esp-cpp/esp-box-emu/boxart/source/aladdin-genesis.jpg

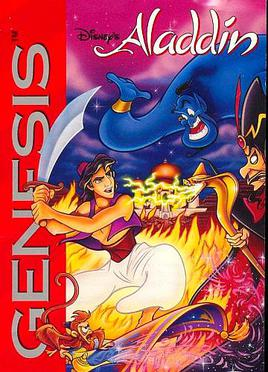
boxart/source/aladdin-genesis.jpg
