esp-cpp/esp-box-emu/boxart/source/aladdin-gg.jpg

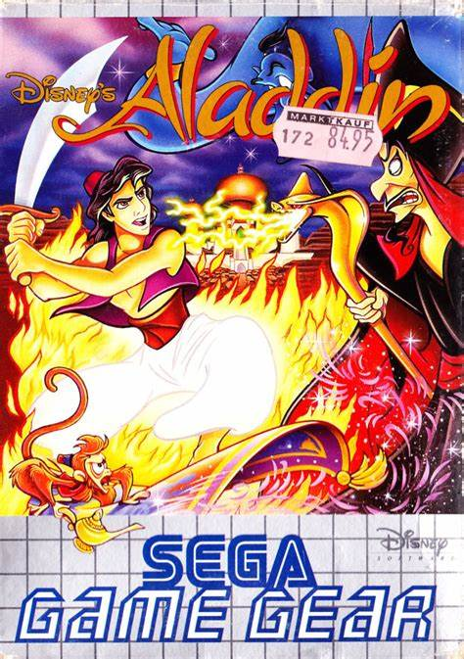
boxart/source/aladdin-gg.jpg
