esp-cpp/esp-box-emu/boxart/source/batman-forever-gg.jpg

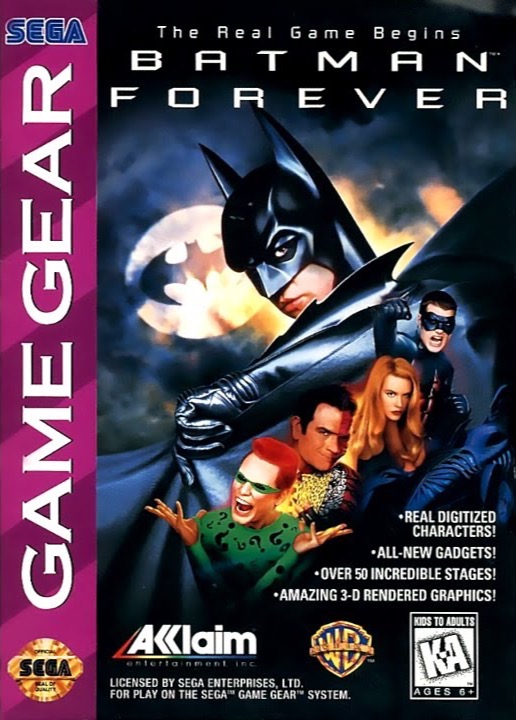
boxart/source/batman-forever-gg.jpg
