esp-cpp/esp-box-emu/boxart/source/batman_the_animated_series.jpg

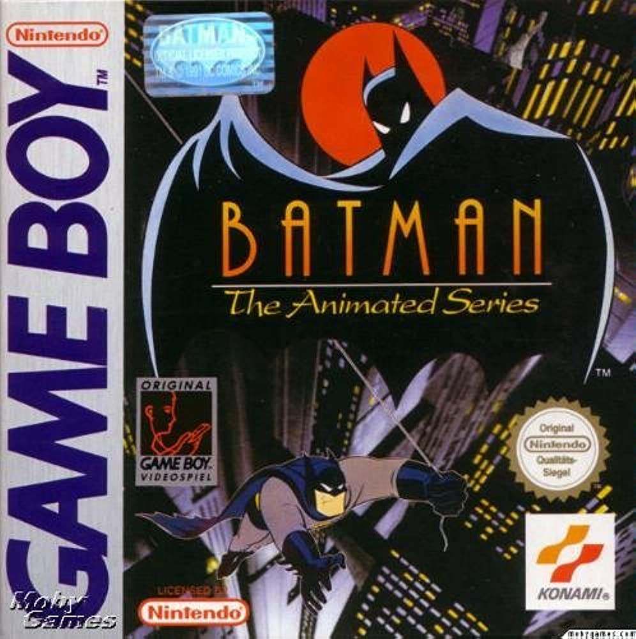
boxart/source/batman_the_animated_series.jpg
