esp-cpp/esp-box-emu/boxart/source/castle-of-illusion-gg.jpg

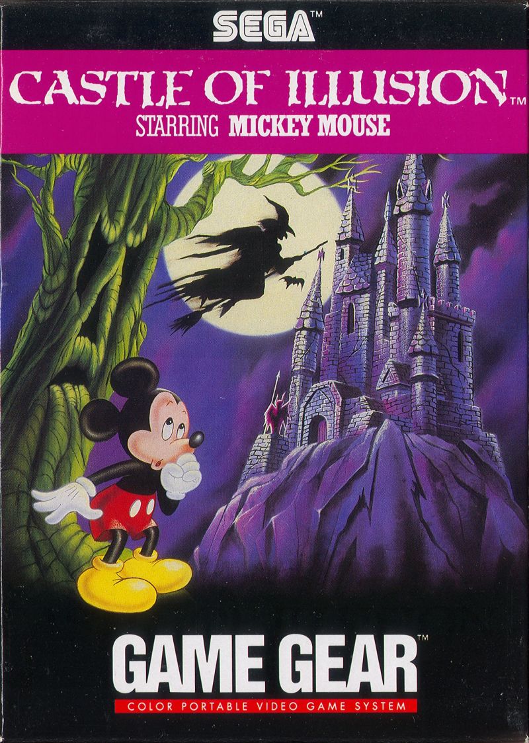
boxart/source/castle-of-illusion-gg.jpg
