esp-cpp/esp-box-emu/boxart/source/chrono_trigger.jpg

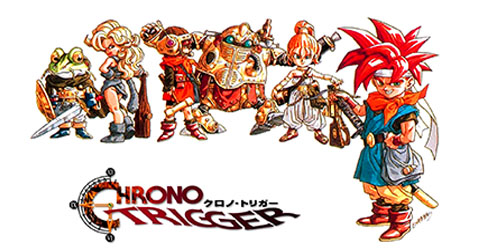
boxart/source/chrono_trigger.jpg
