esp-cpp/esp-box-emu/boxart/source/donkey_kong_country.jpg

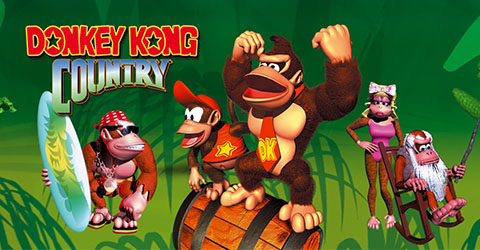
boxart/source/donkey_kong_country.jpg
