esp-cpp/esp-box-emu/boxart/source/doom_2_boxart.jpg

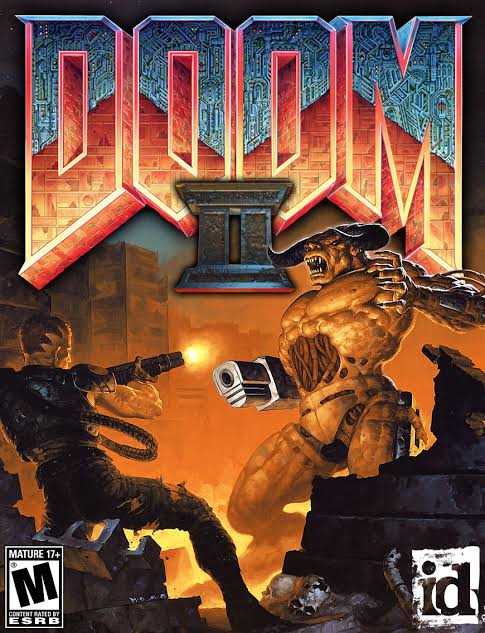
boxart/source/doom_2_boxart.jpg
