esp-cpp/esp-box-emu/boxart/source/doom_boxart.jpg

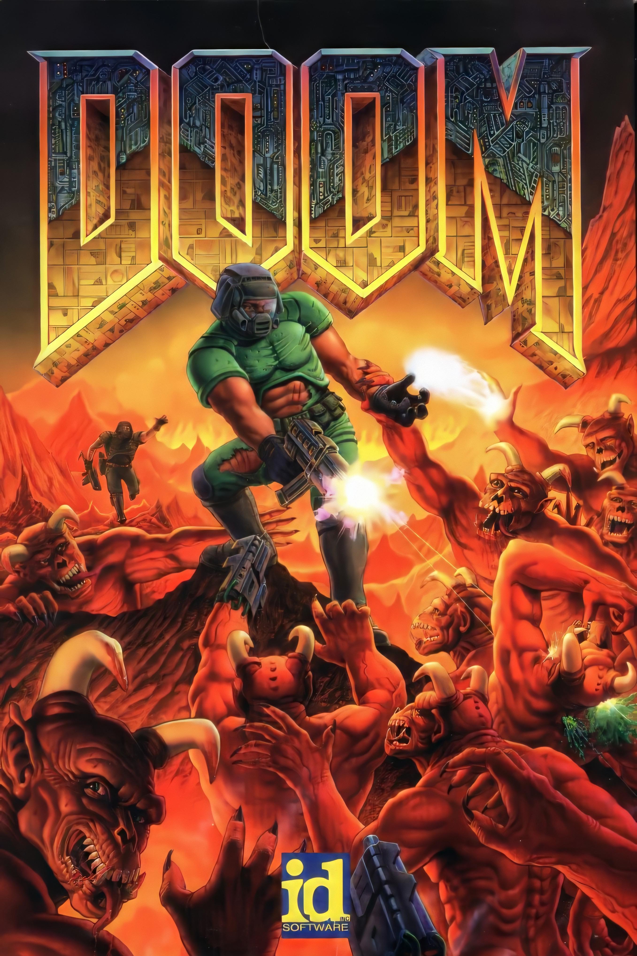
boxart/source/doom_boxart.jpg
