esp-cpp/esp-box-emu/boxart/source/doom_ultimate_boxart.jpg

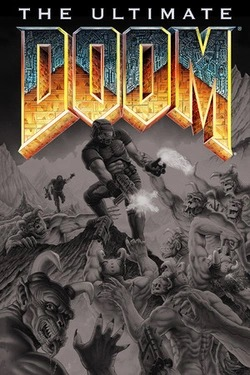
boxart/source/doom_ultimate_boxart.jpg
