esp-cpp/esp-box-emu/boxart/source/duck_tales.jpg

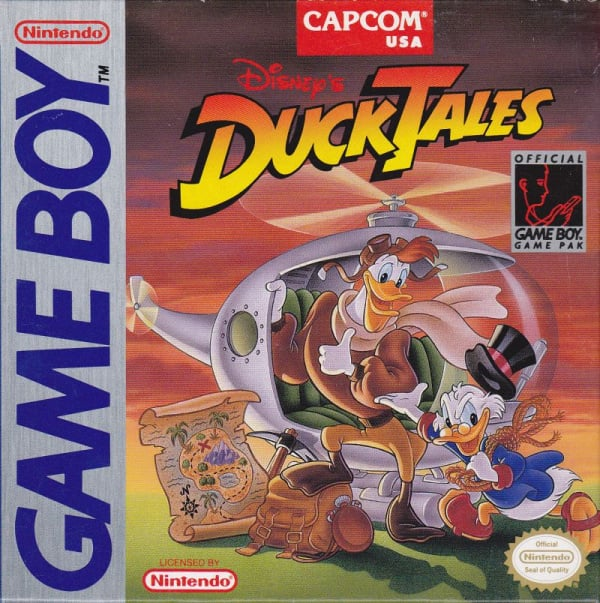
boxart/source/duck_tales.jpg
