esp-cpp/esp-box-emu/boxart/source/ducktales_nes.jpg

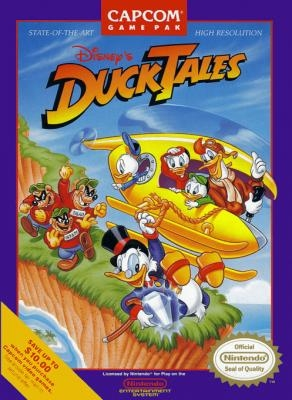
boxart/source/ducktales_nes.jpg
