esp-cpp/esp-box-emu/boxart/source/final_fantasy.jpg

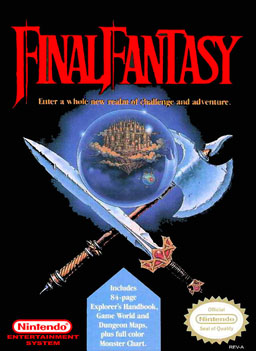
boxart/source/final_fantasy.jpg
