esp-cpp/esp-box-emu/boxart/source/final_fantasy_adventure.jpg

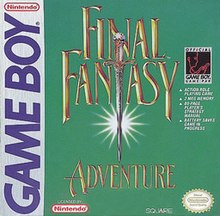
boxart/source/final_fantasy_adventure.jpg
