esp-cpp/esp-box-emu/boxart/source/final_fantasy_ii.jpg

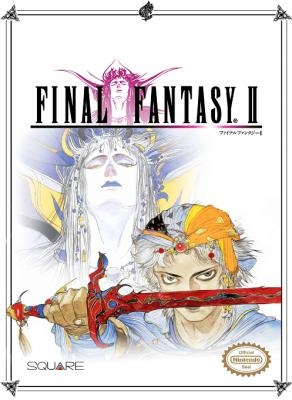
boxart/source/final_fantasy_ii.jpg
