esp-cpp/esp-box-emu/boxart/source/final_fantasy_iii.jpg

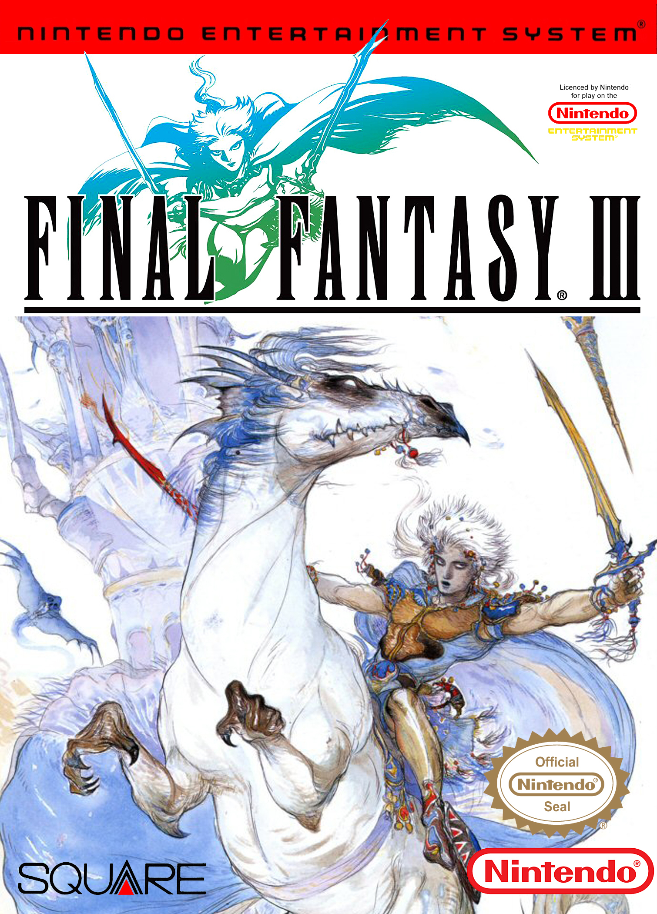
boxart/source/final_fantasy_iii.jpg
