esp-cpp/esp-box-emu/boxart/source/ghouls-n-ghosts-sms.jpg

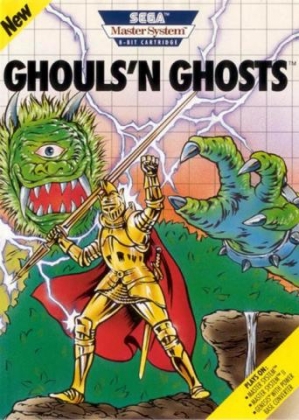
boxart/source/ghouls-n-ghosts-sms.jpg
