esp-cpp/esp-box-emu/boxart/source/harvest_moon.jpg

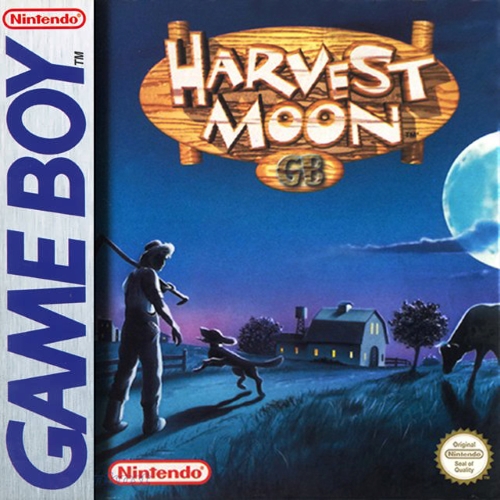
boxart/source/harvest_moon.jpg
