esp-cpp/esp-box-emu/boxart/source/harvest_moon_gbc.jpg

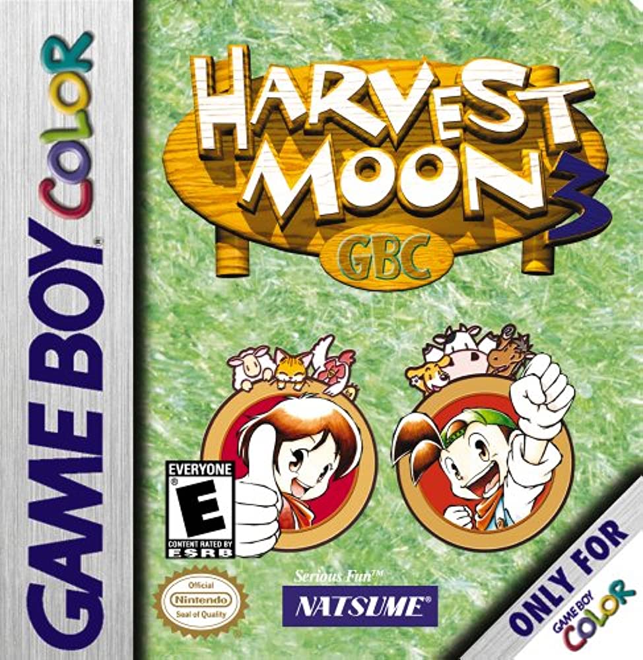
boxart/source/harvest_moon_gbc.jpg
