esp-cpp/esp-box-emu/boxart/source/jurassic-park-gg.jpg

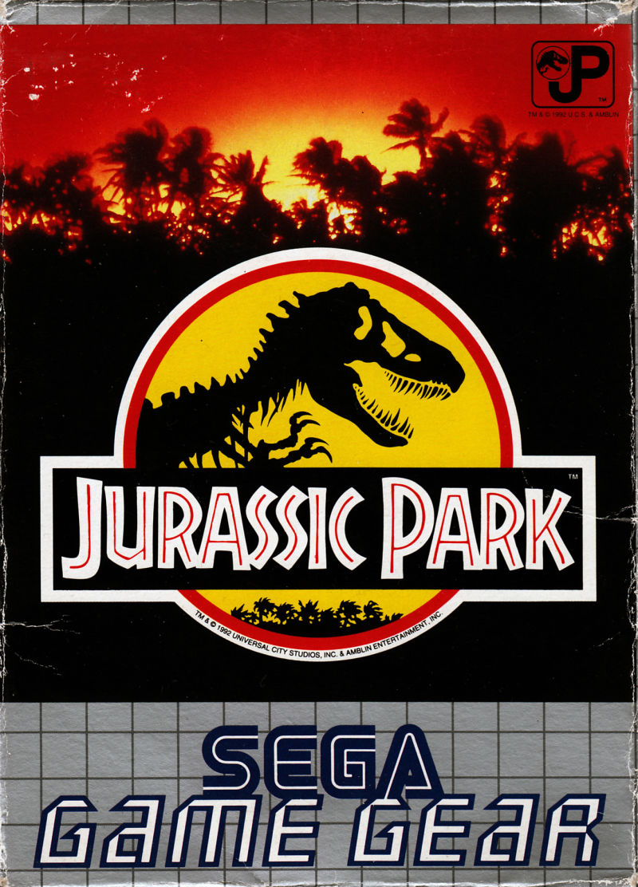
boxart/source/jurassic-park-gg.jpg
