esp-cpp/esp-box-emu/boxart/source/lion-king-genesis.jpg

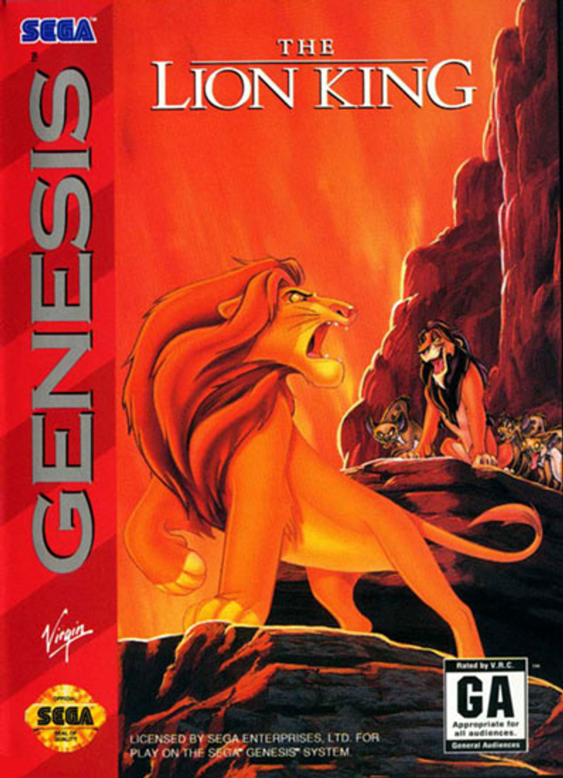
boxart/source/lion-king-genesis.jpg
