esp-cpp/esp-box-emu/boxart/source/mario.jpg

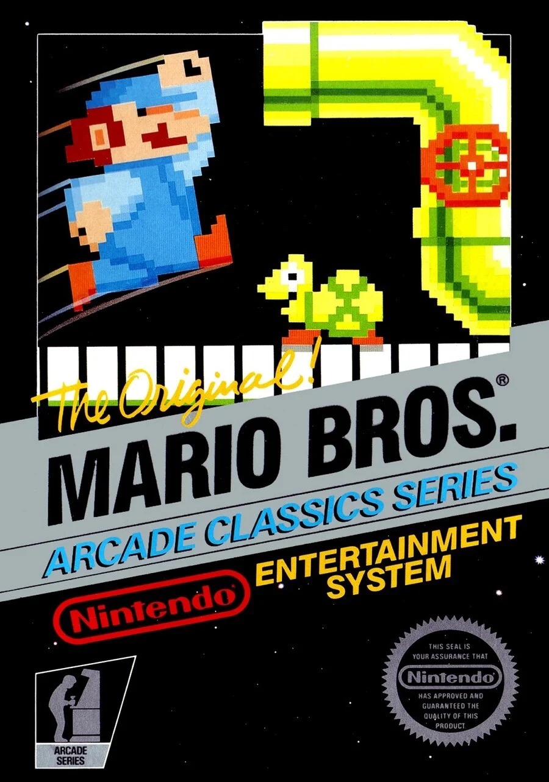
boxart/source/mario.jpg
