esp-cpp/esp-box-emu/boxart/source/mario_golf.jpg

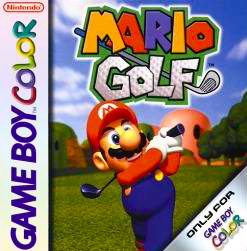
boxart/source/mario_golf.jpg
