esp-cpp/esp-box-emu/boxart/source/mario_open_golf.jpg

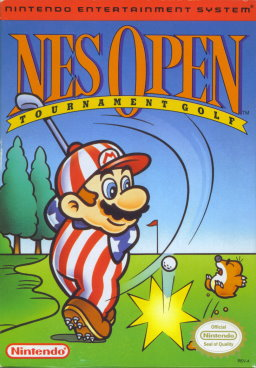
boxart/source/mario_open_golf.jpg
