esp-cpp/esp-box-emu/boxart/source/mario_tennis.jpg

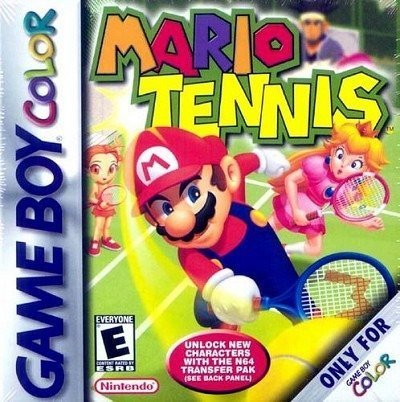
boxart/source/mario_tennis.jpg
