esp-cpp/esp-box-emu/boxart/source/megaman1.jpg

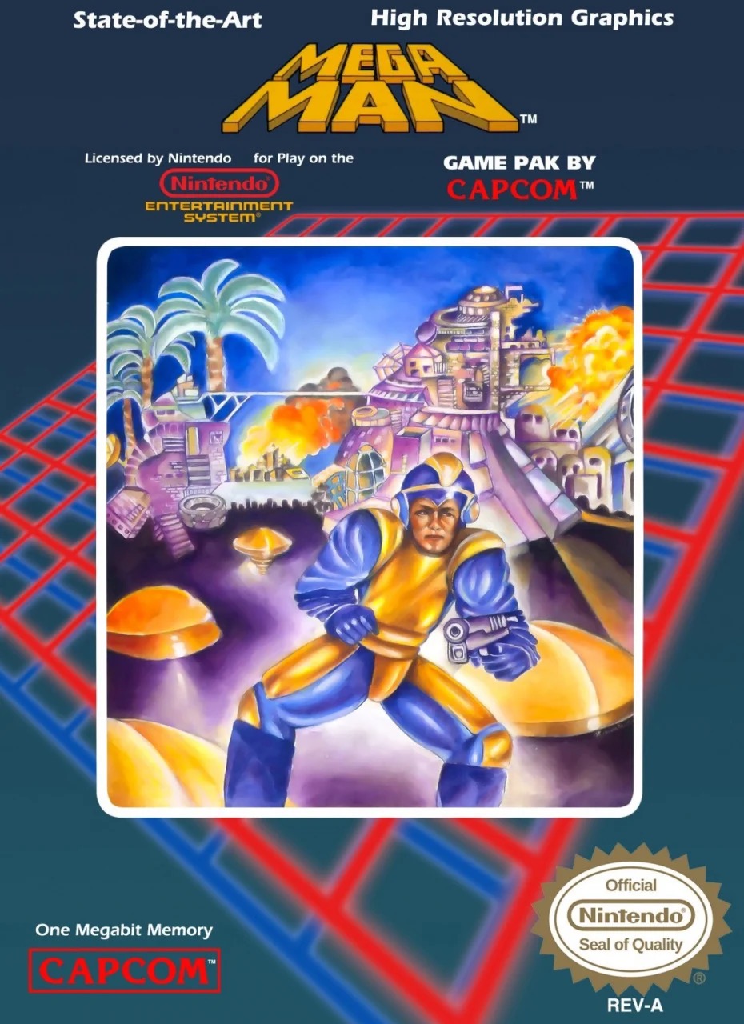
boxart/source/megaman1.jpg
