esp-cpp/esp-box-emu/boxart/source/metal_gear.jpg

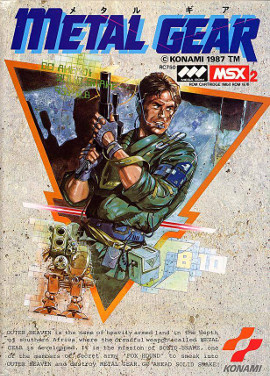
boxart/source/metal_gear.jpg
