esp-cpp/esp-box-emu/boxart/source/metal_gear_solid.jpg

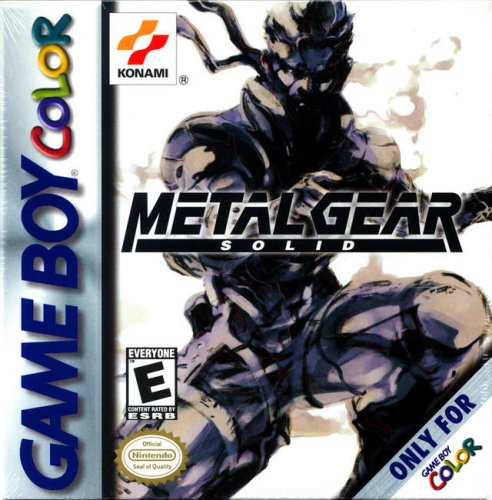
boxart/source/metal_gear_solid.jpg
