esp-cpp/esp-box-emu/boxart/source/metroid1.jpg

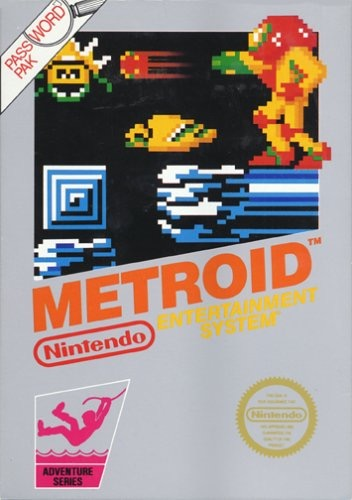
boxart/source/metroid1.jpg
