esp-cpp/esp-box-emu/boxart/source/metroid_2_return_of_samus.jpg

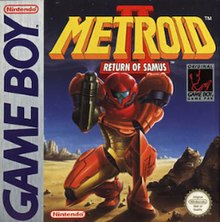
boxart/source/metroid_2_return_of_samus.jpg
