esp-cpp/esp-box-emu/boxart/source/mg1msxartwork.jpg

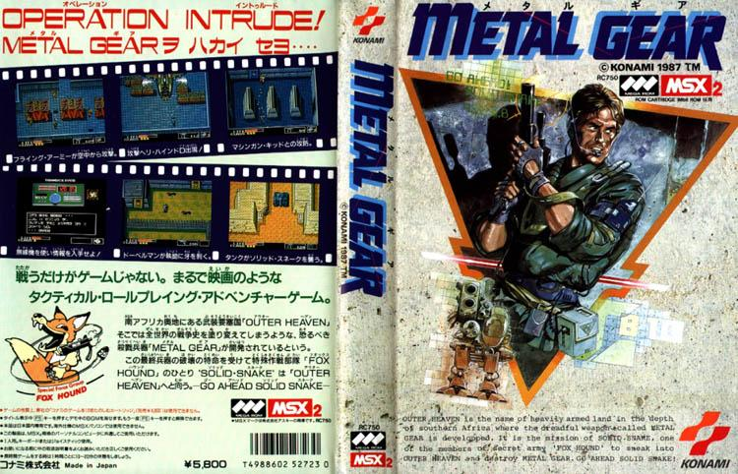
boxart/source/mg1msxartwork.jpg
