esp-cpp/esp-box-emu/boxart/source/mg2msxartwork.jpg

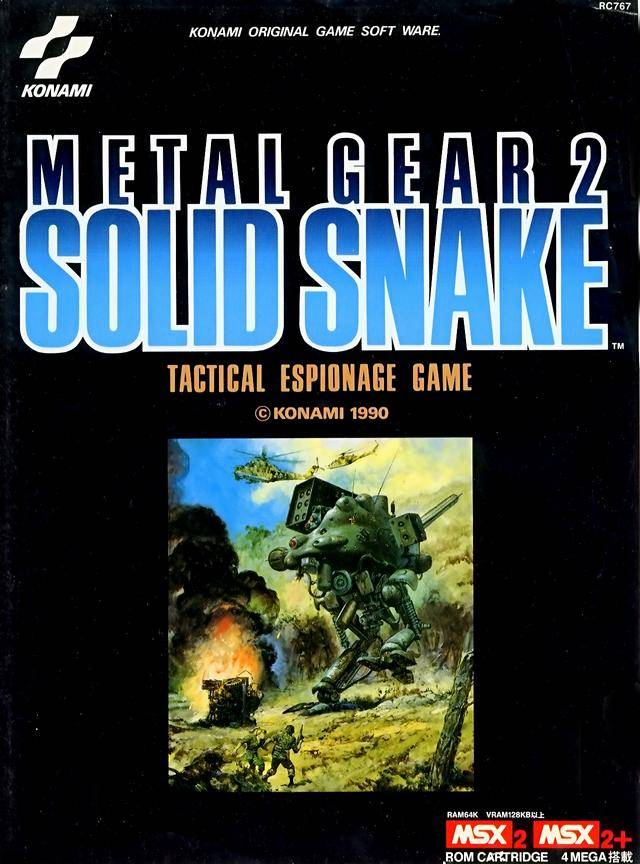
boxart/source/mg2msxartwork.jpg
