esp-cpp/esp-box-emu/boxart/source/Ninja+Gaiden+(Europe)-sms.jpg

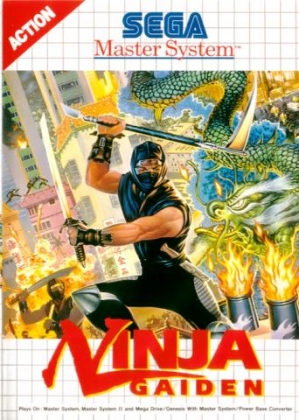
boxart/source/Ninja+Gaiden+(Europe)-sms.jpg
