esp-cpp/esp-box-emu/boxart/source/Out+Run+(Europe)-gg.jpg

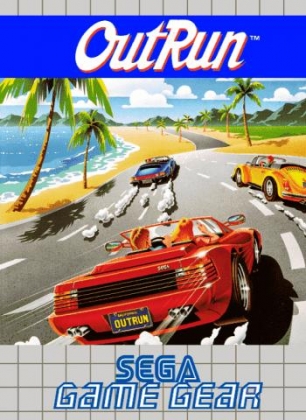
boxart/source/Out+Run+(Europe)-gg.jpg
