esp-cpp/esp-box-emu/boxart/source/Out+Run+(World)-sms.jpg

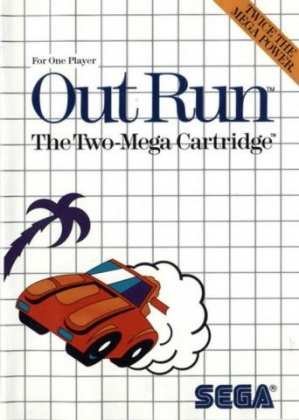
boxart/source/Out+Run+(World)-sms.jpg
