esp-cpp/esp-box-emu/boxart/source/Out+Run+Europa+gg.jpg

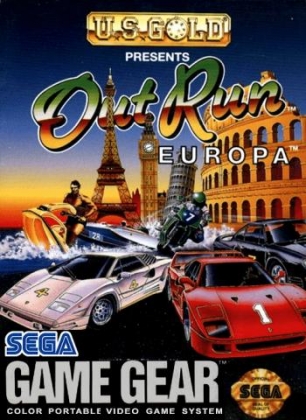
boxart/source/Out+Run+Europa+gg.jpg
