esp-cpp/esp-box-emu/boxart/source/pokemon_blue.jpg

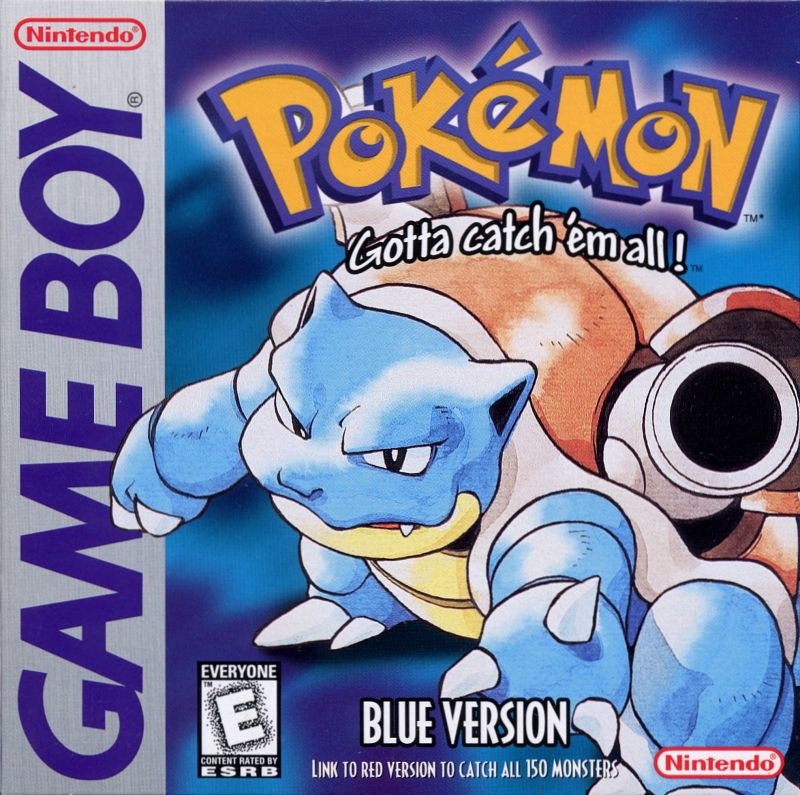
boxart/source/pokemon_blue.jpg
