esp-cpp/esp-box-emu/boxart/source/pokemon_crystal.jpg

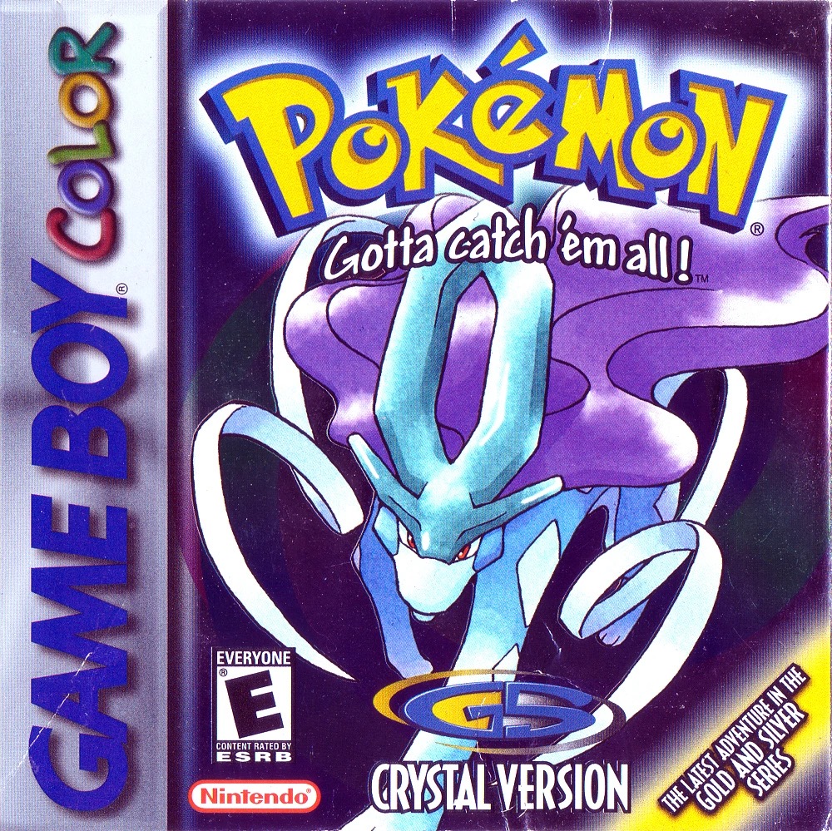
boxart/source/pokemon_crystal.jpg
