esp-cpp/esp-box-emu/boxart/source/pokemon_red.jpg

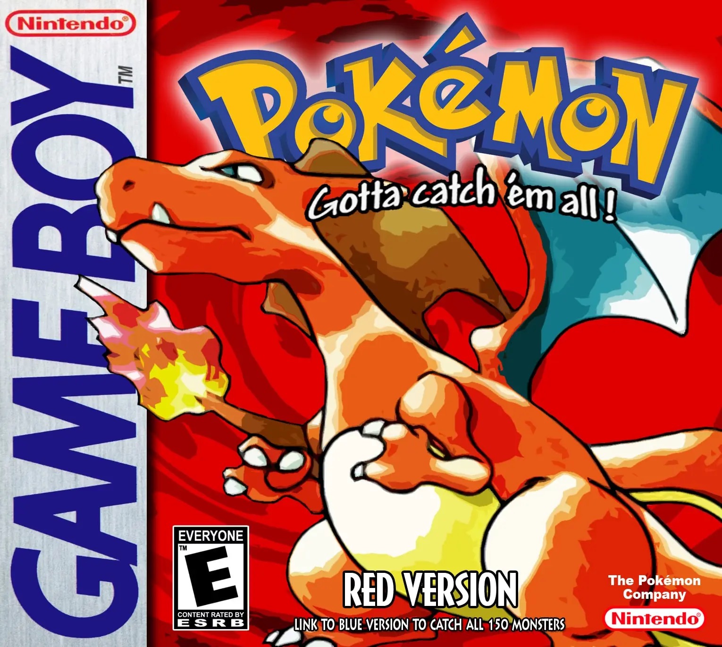
boxart/source/pokemon_red.jpg
