esp-cpp/esp-box-emu/boxart/source/R-Type-sms.jpg

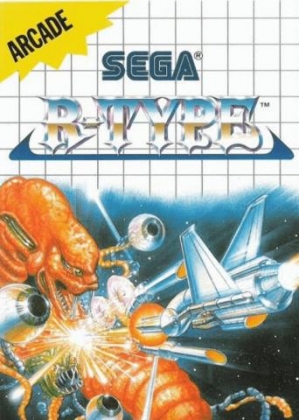
boxart/source/R-Type-sms.jpg
