esp-cpp/esp-box-emu/boxart/source/river-city-ransom.jpg

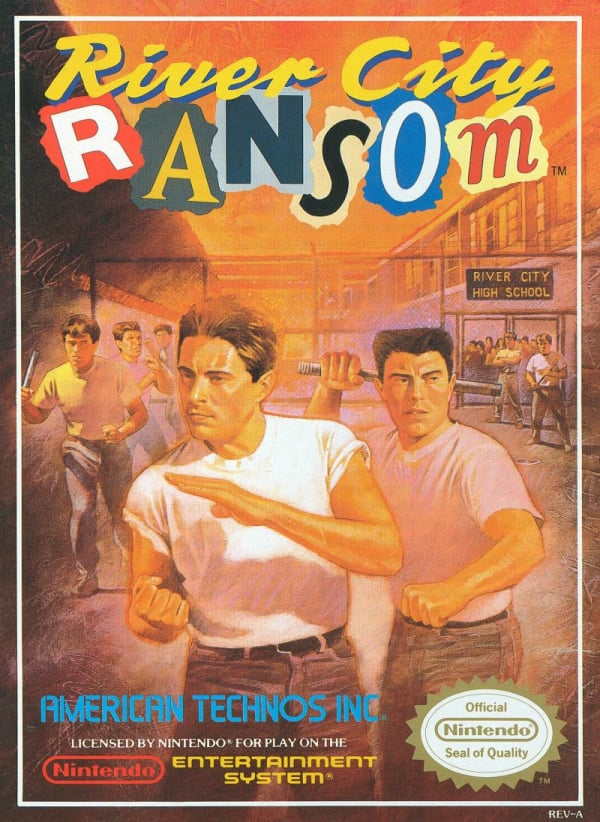
boxart/source/river-city-ransom.jpg
