esp-cpp/esp-box-emu/boxart/source/Road+Rash+(USA)-gg.jpg

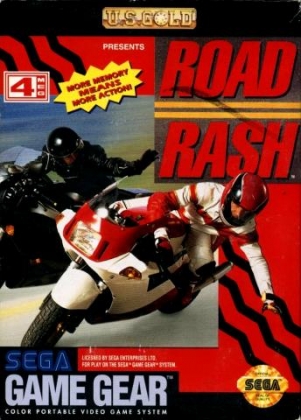
boxart/source/Road+Rash+(USA)-gg.jpg
