esp-cpp/esp-box-emu/boxart/source/shantae.jpg

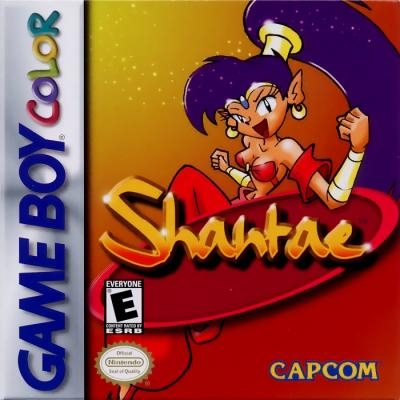
boxart/source/shantae.jpg
