esp-cpp/esp-box-emu/boxart/source/sonic-1-genesis.jpg

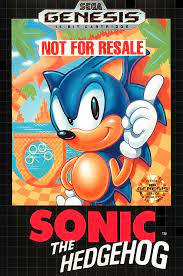
boxart/source/sonic-1-genesis.jpg
