esp-cpp/esp-box-emu/boxart/source/sonic-2-genesis.jpg

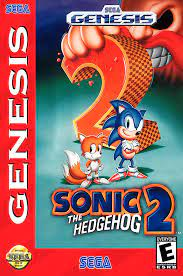
boxart/source/sonic-2-genesis.jpg
