esp-cpp/esp-box-emu/boxart/source/sonic-3-and-knuckles.jpg

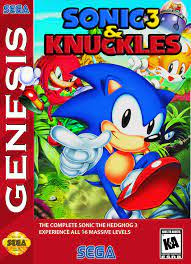
boxart/source/sonic-3-and-knuckles.jpg
