esp-cpp/esp-box-emu/boxart/source/sonic-3-genesis.jpg

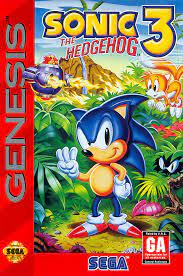
boxart/source/sonic-3-genesis.jpg
