esp-cpp/esp-box-emu/boxart/source/sonic-and-knuckles-genesis.jpg

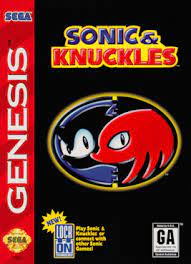
boxart/source/sonic-and-knuckles-genesis.jpg
