esp-cpp/esp-box-emu/boxart/source/sonic-the-hedgehog-2-gg.jpg

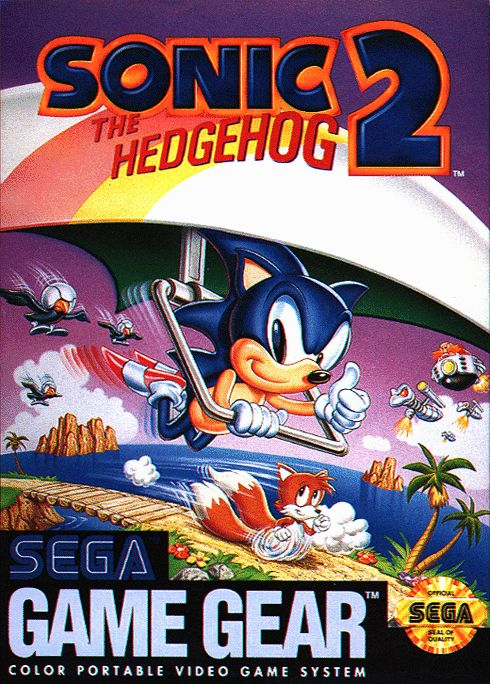
boxart/source/sonic-the-hedgehog-2-gg.jpg
