esp-cpp/esp-box-emu/boxart/source/sonic-the-hedgehog-2-sms.jpg

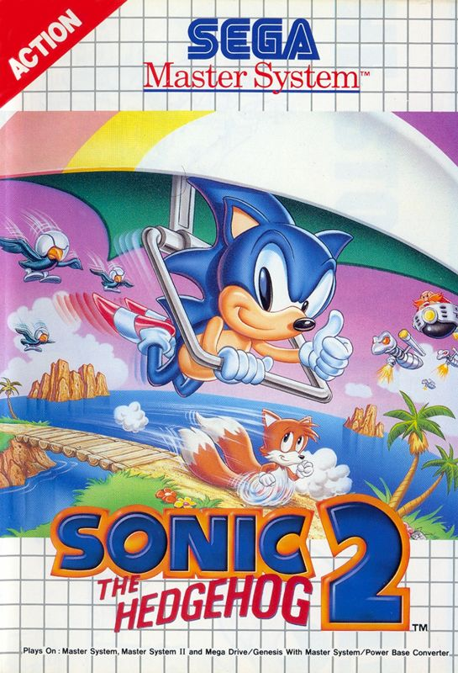
boxart/source/sonic-the-hedgehog-2-sms.jpg
