esp-cpp/esp-box-emu/boxart/source/spider-man-and-venom-maximum-carnage.jpg

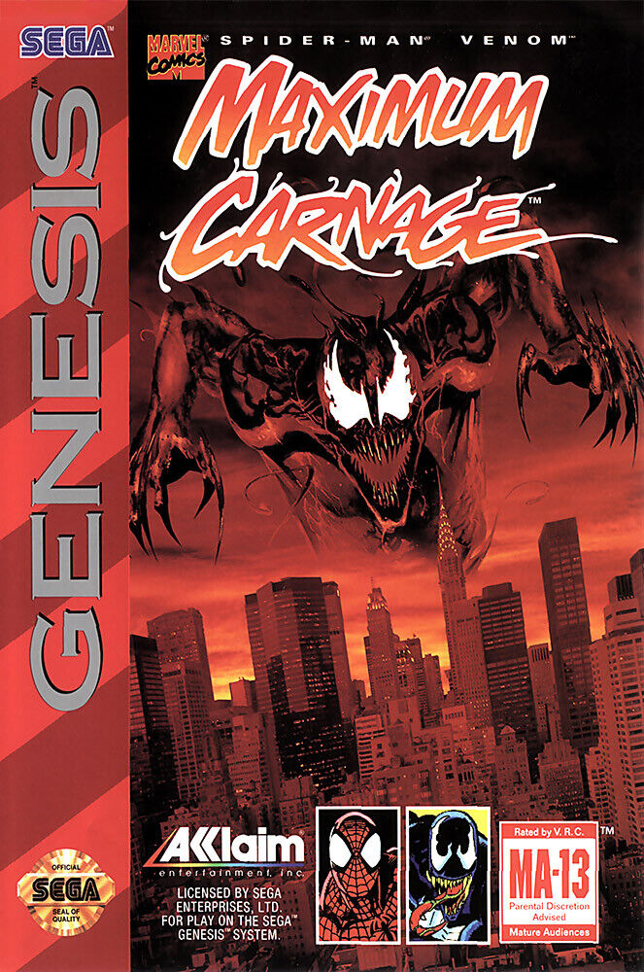
boxart/source/spider-man-and-venom-maximum-carnage.jpg
