esp-cpp/esp-box-emu/boxart/source/Star-Trek-Generations-Beyond-the-Nexus-gg.jpg

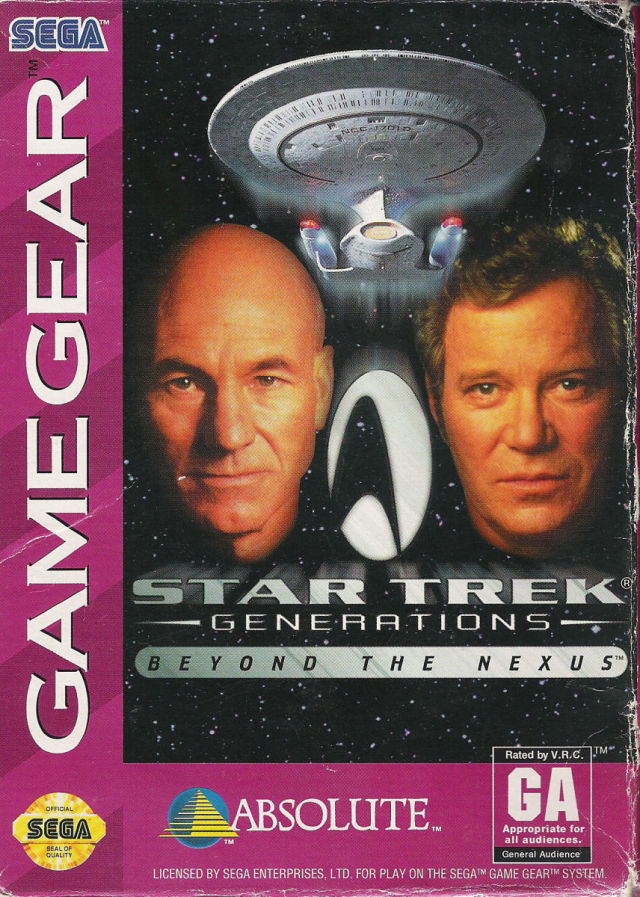
boxart/source/Star-Trek-Generations-Beyond-the-Nexus-gg.jpg
