esp-cpp/esp-box-emu/boxart/source/star_wars_arcade_32x_genesis.jpg

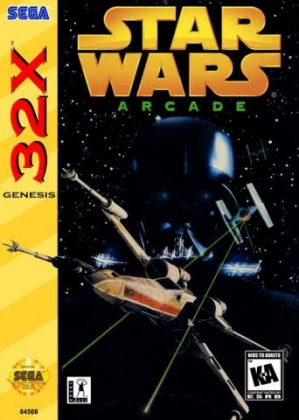
boxart/source/star_wars_arcade_32x_genesis.jpg
