esp-cpp/esp-box-emu/boxart/source/StreetsofRage2-gg.jpg

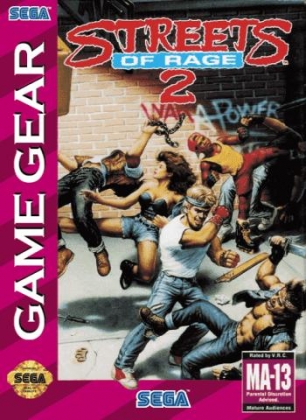
boxart/source/StreetsofRage2-gg.jpg
