esp-cpp/esp-box-emu/boxart/source/super_mario_bros_1.jpg

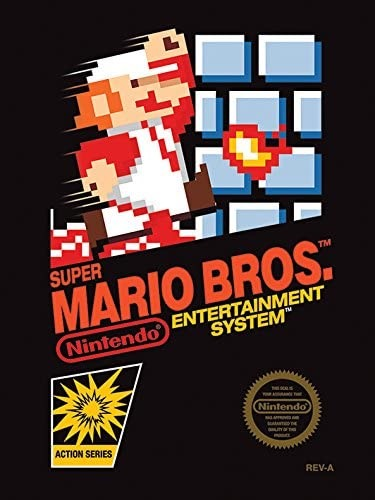
boxart/source/super_mario_bros_1.jpg
