esp-cpp/esp-box-emu/boxart/source/super_mario_bros_2.jpg

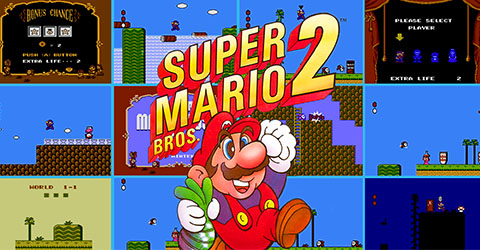
boxart/source/super_mario_bros_2.jpg
