esp-cpp/esp-box-emu/boxart/source/super_mario_bros_3.jpg

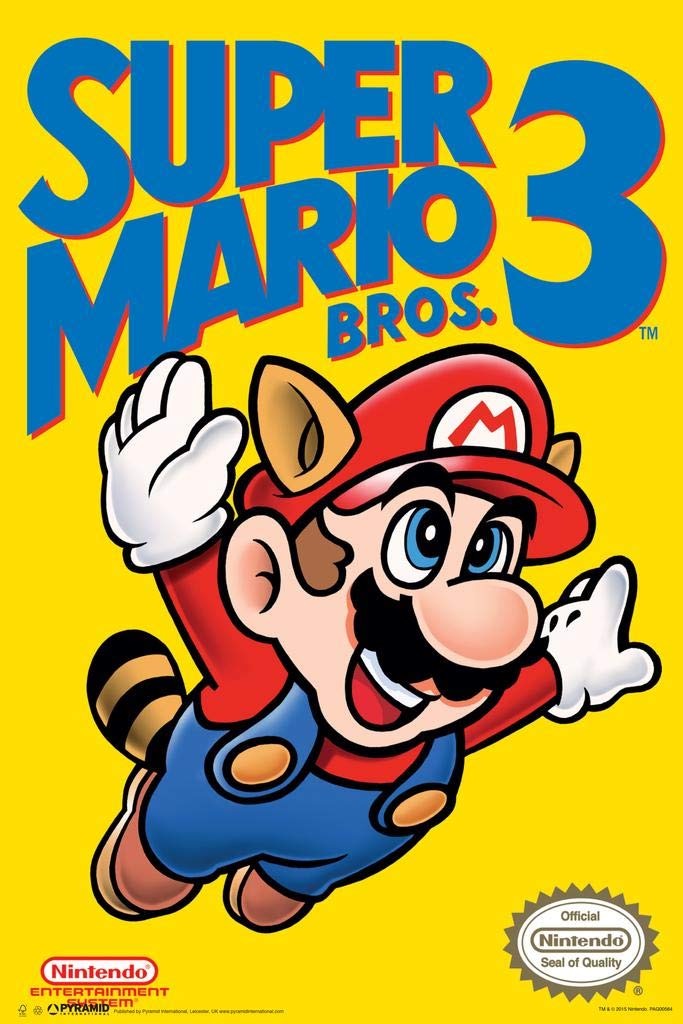
boxart/source/super_mario_bros_3.jpg
