esp-cpp/esp-box-emu/boxart/source/super_mario_bros_deluxe.jpg

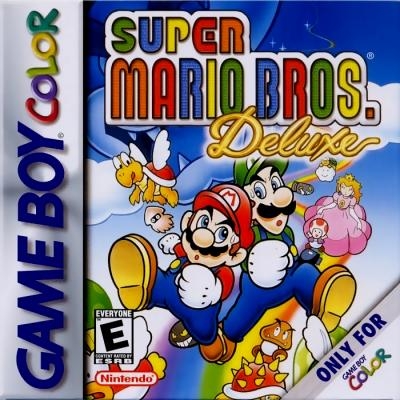
boxart/source/super_mario_bros_deluxe.jpg
