esp-cpp/esp-box-emu/boxart/source/tetris_dx.jpg

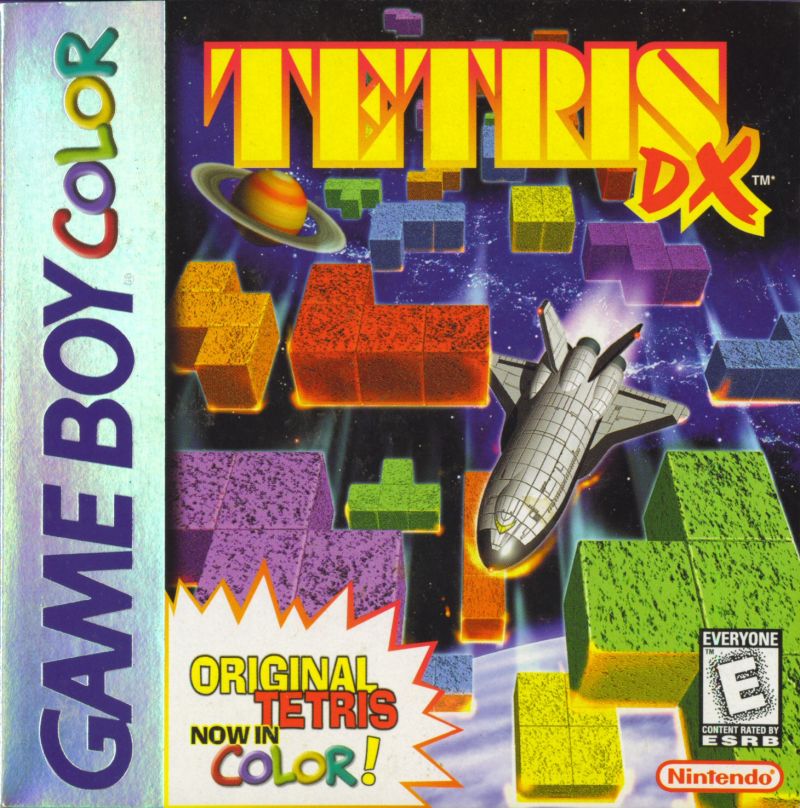
boxart/source/tetris_dx.jpg
