esp-cpp/esp-box-emu/boxart/source/The-Adventures-of-Batman-and-Robin-Game-Gear.jpg

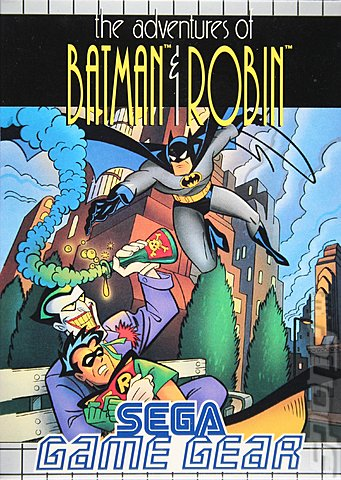
boxart/source/The-Adventures-of-Batman-and-Robin-Game-Gear.jpg
