esp-cpp/esp-box-emu/boxart/source/tloz_links_awakening.jpg

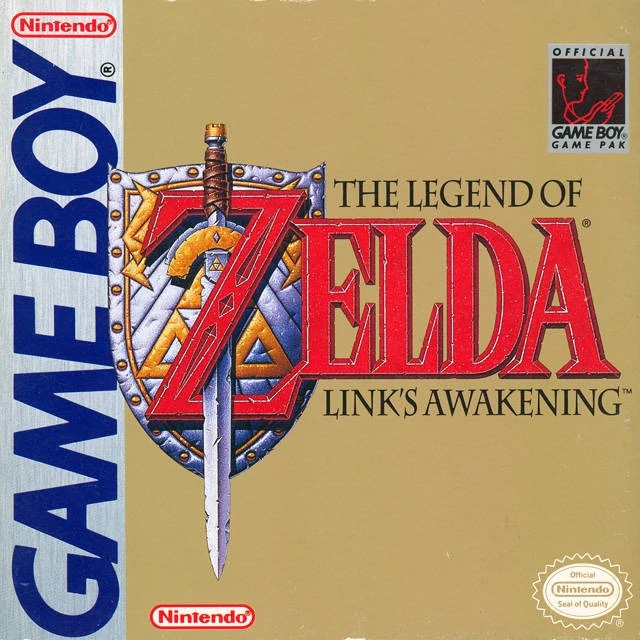
boxart/source/tloz_links_awakening.jpg
