esp-cpp/esp-box-emu/boxart/source/tloz_links_awakening_dx.jpg

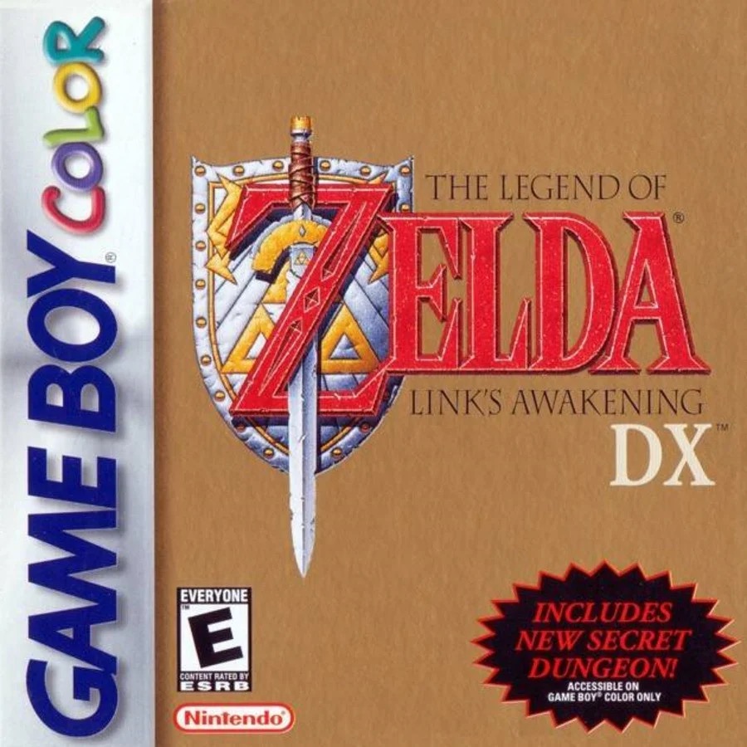
boxart/source/tloz_links_awakening_dx.jpg
