esp-cpp/esp-box-emu/boxart/source/tloz_oracle_ages.jpg

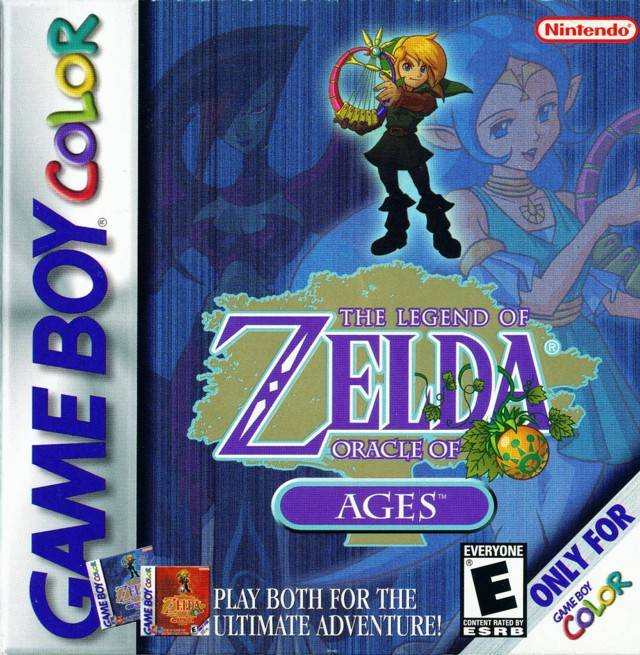
boxart/source/tloz_oracle_ages.jpg
