esp-cpp/esp-box-emu/boxart/source/tloz_oracle_seasons.jpg

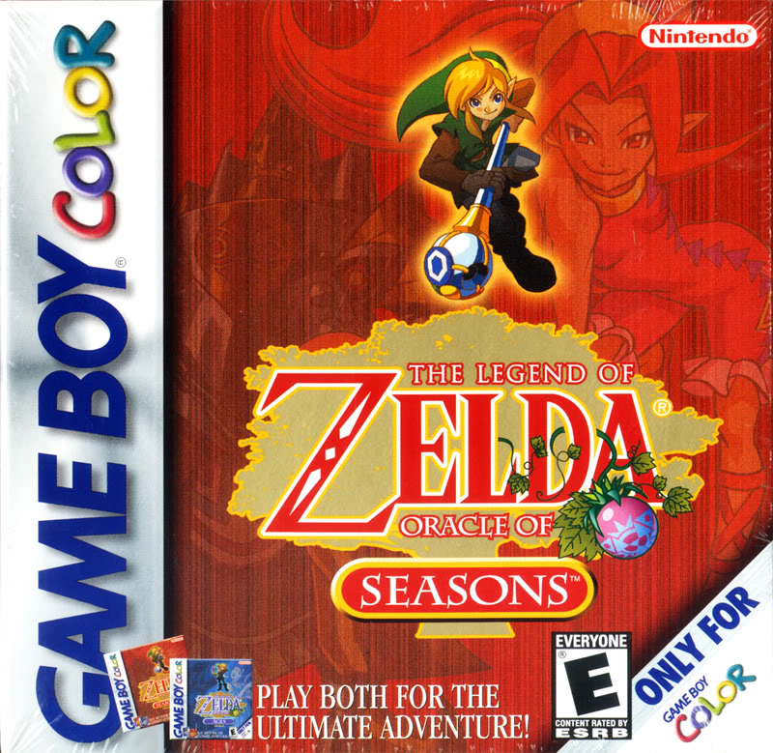
boxart/source/tloz_oracle_seasons.jpg
