esp-cpp/esp-box-emu/boxart/source/toy-story-genesis.jpg

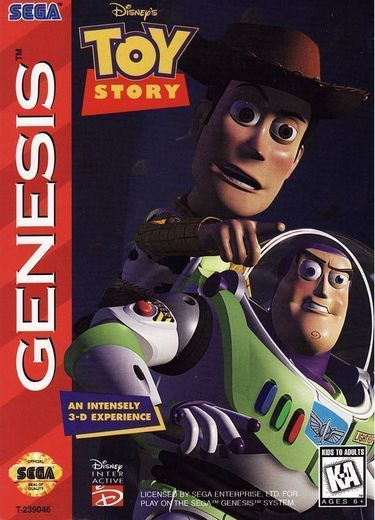
boxart/source/toy-story-genesis.jpg
