esp-cpp/esp-box-emu/boxart/source/wonder-boy-iii-dragon-trap-gg.jpg

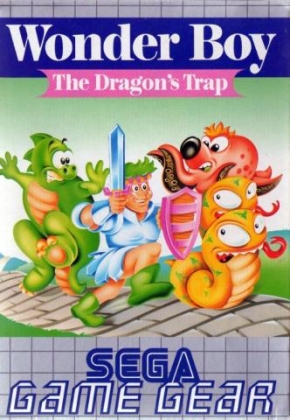
boxart/source/wonder-boy-iii-dragon-trap-gg.jpg
