esp-cpp/esp-box-emu/boxart/source/wonder-boy-iii-dragon-trap-sms.jpg

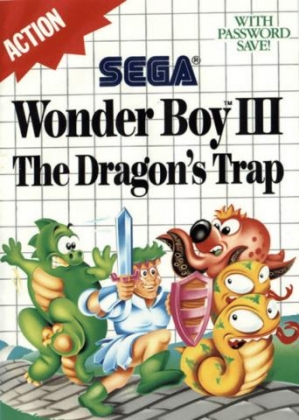
boxart/source/wonder-boy-iii-dragon-trap-sms.jpg
