esp-cpp/esp-box-emu/boxart/source/zelda1.jpg

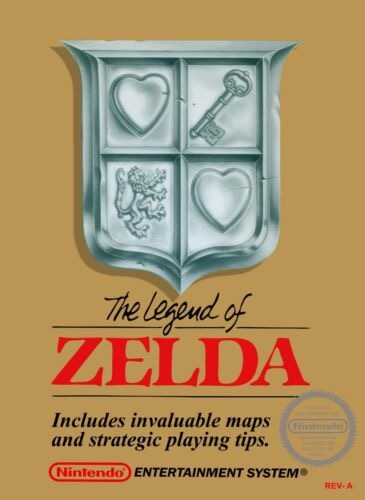
boxart/source/zelda1.jpg
