esp-cpp/esp-box-emu/boxart/source/zelda2.jpg

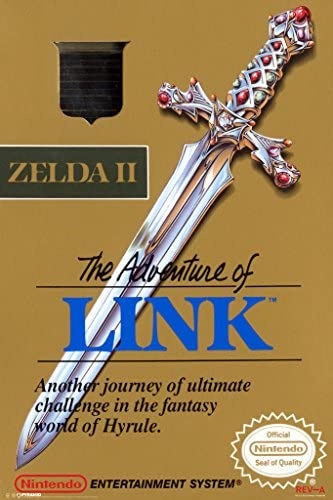
boxart/source/zelda2.jpg
