esp-cpp/esp-box-emu/images/box-emu-cad-with-s3-box.png

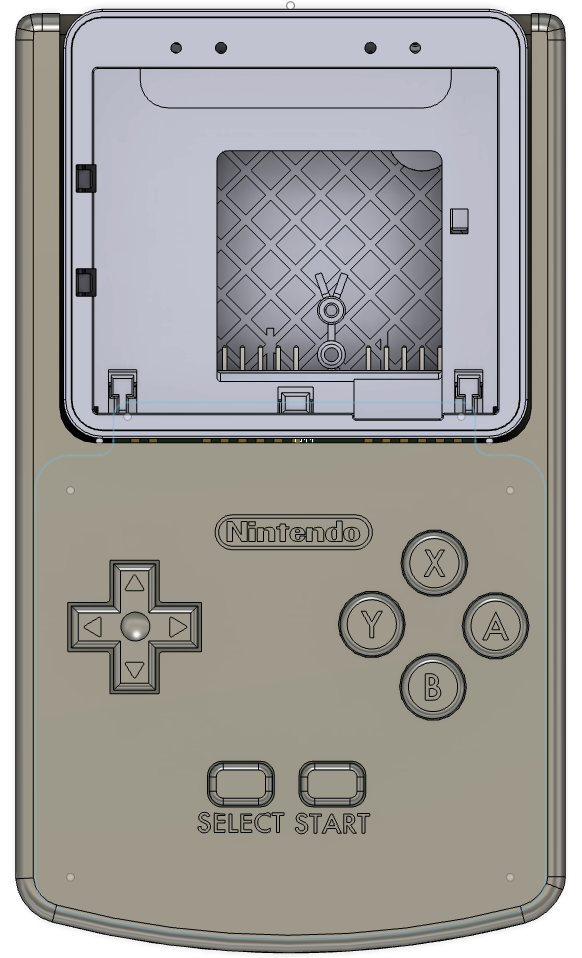
images/box-emu-cad-with-s3-box.png
