esp-cpp/esp-box-emu/images/electronics-1.jpg

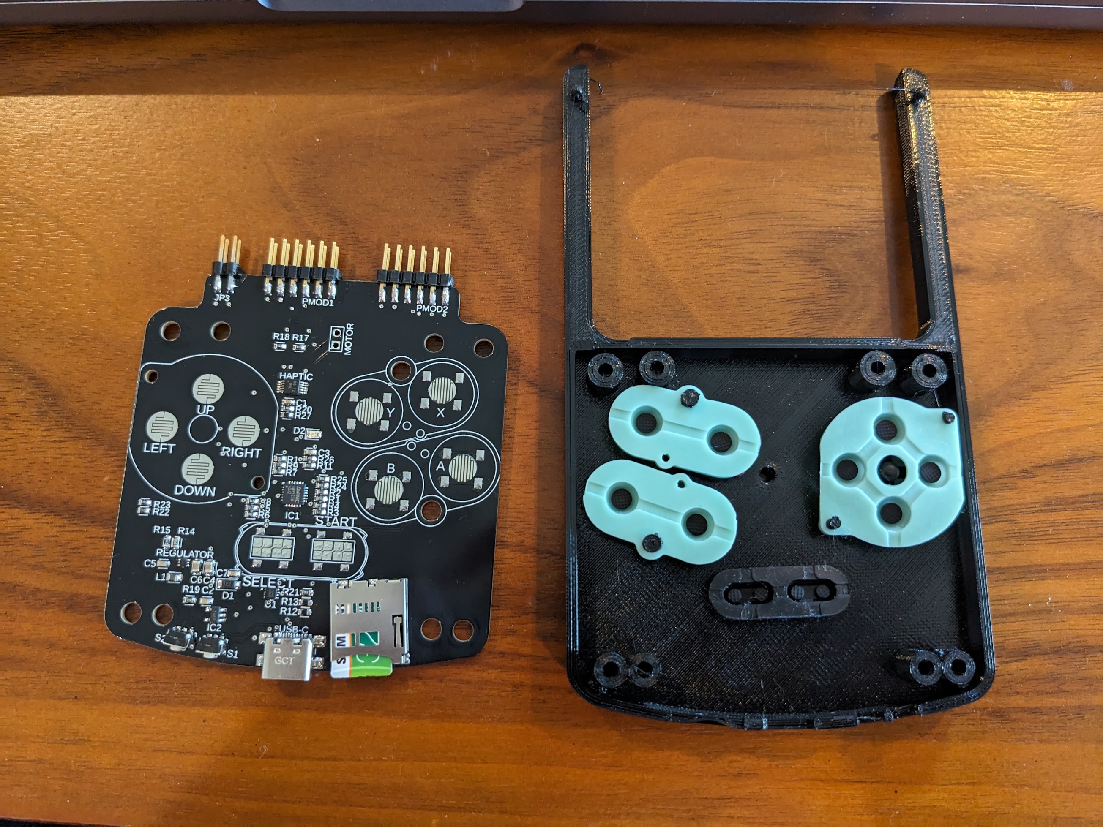
images/electronics-1.jpg
