esp-cpp/esp-box-emu/images/electronics-vbat-trace.png

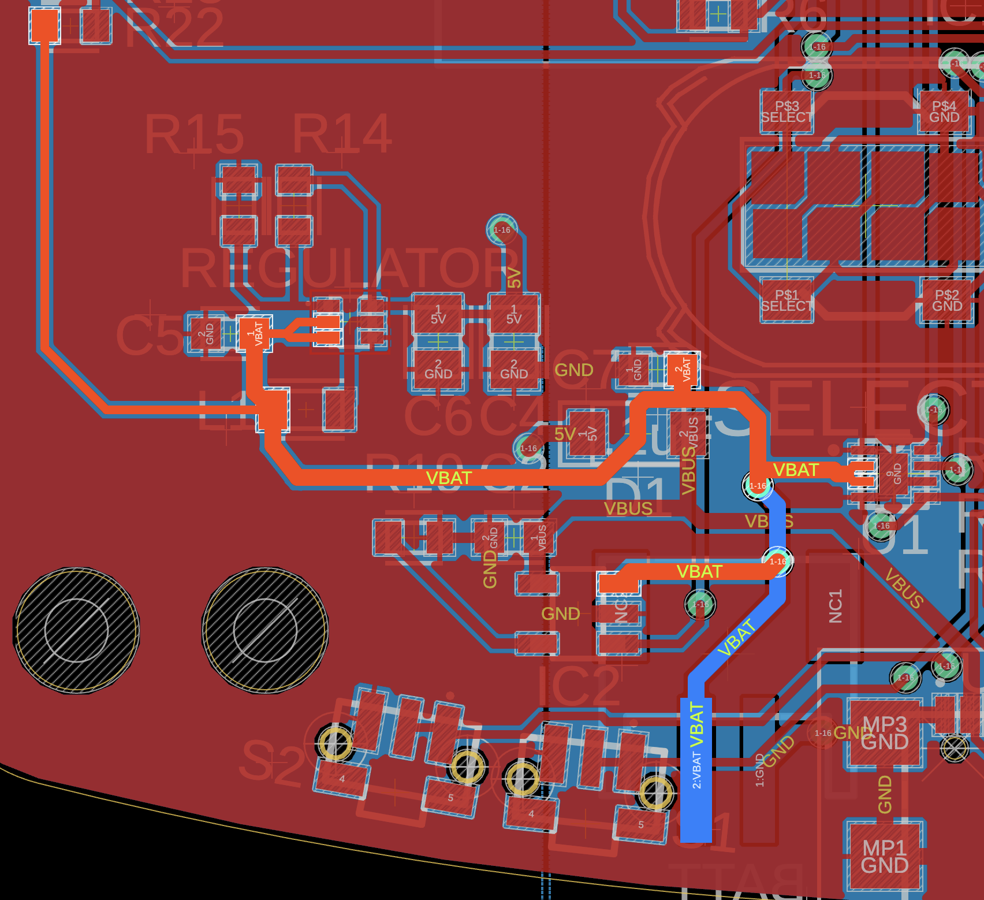
images/electronics-vbat-trace.png
