esp-cpp/esp-box-emu/images/emu_v1.jpg

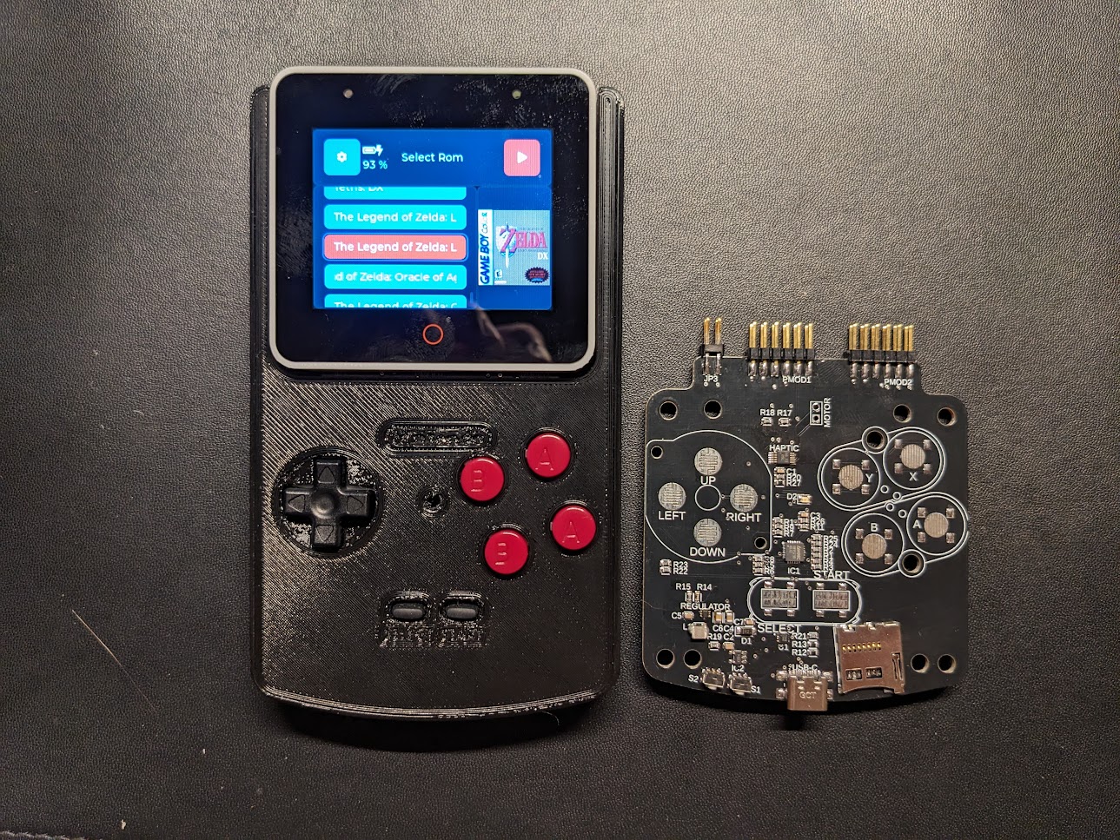
images/emu_v1.jpg
