esp-cpp/esp-box-emu/images/emu_v1_pcb_closeup.jpg

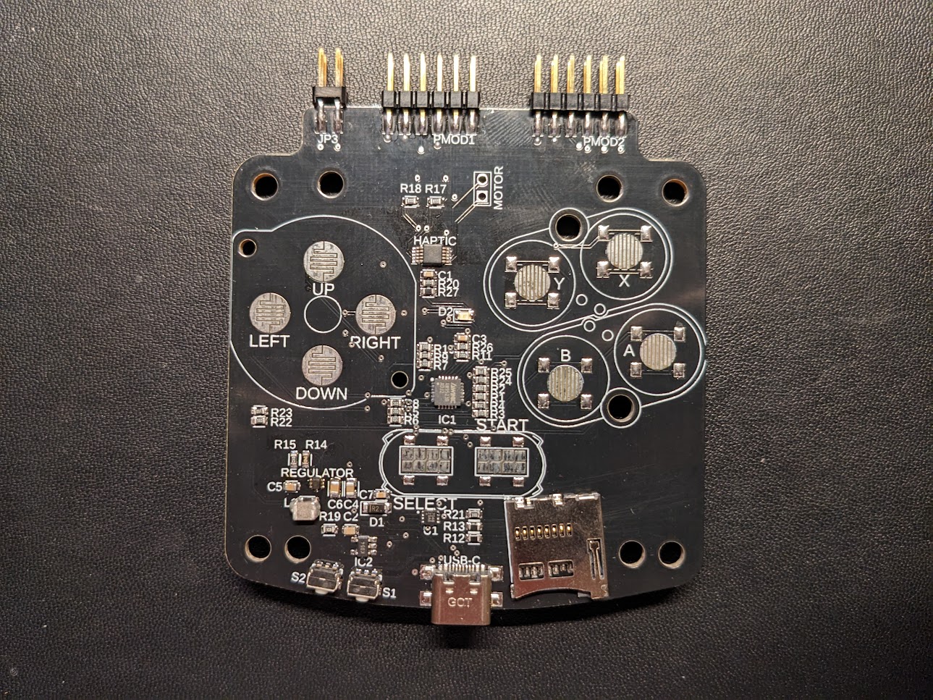
images/emu_v1_pcb_closeup.jpg
