esp-cpp/esp-box-emu/images/esp-box-emu-3-top-cover-hidden.png

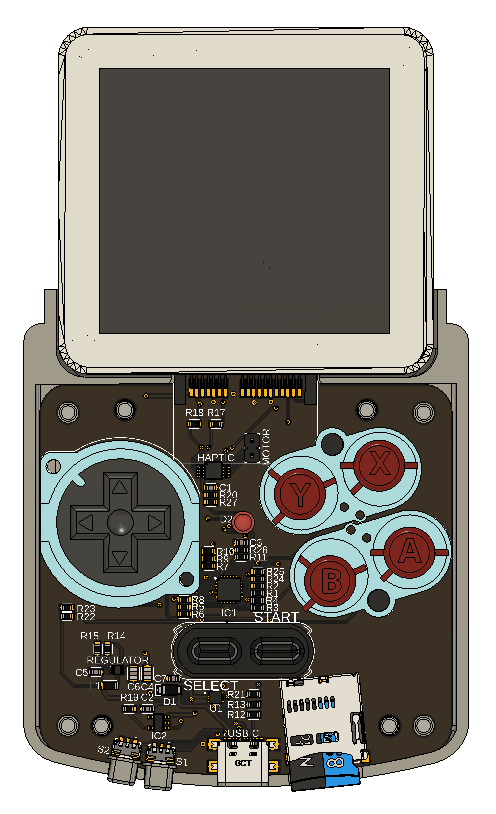
images/esp-box-emu-3-top-cover-hidden.png
