esp-cpp/esp-box-emu/images/esp-box-emu-top-cover-hidden.png

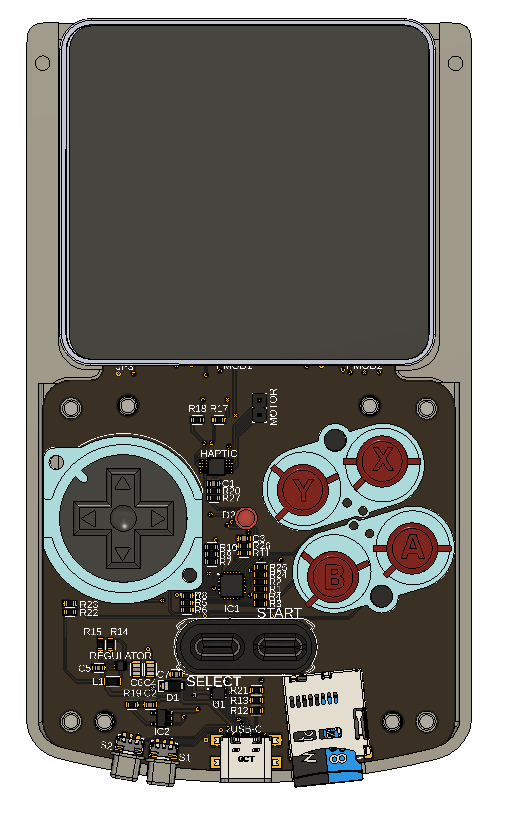
images/esp-box-emu-top-cover-hidden.png
