esp-cpp/esp-box-emu/mcad/gbc/decal cristal.png

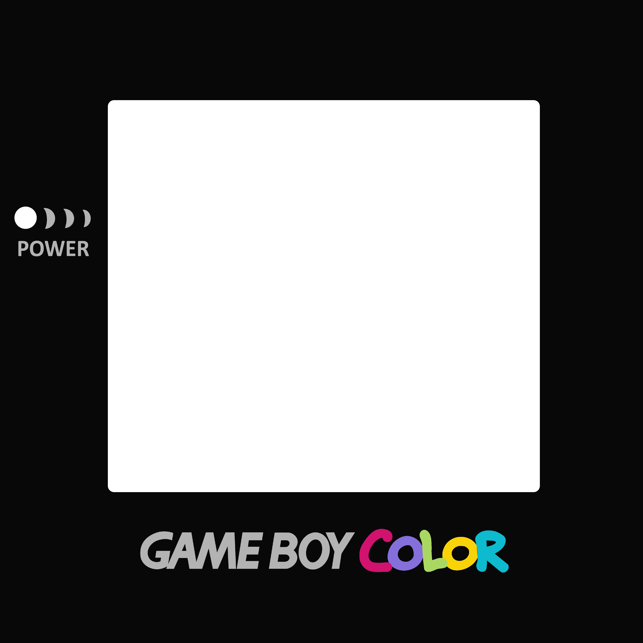
mcad/gbc/decal cristal.png
