esp-cpp/esp-box-emu/mcad/gbc/decal numero.png

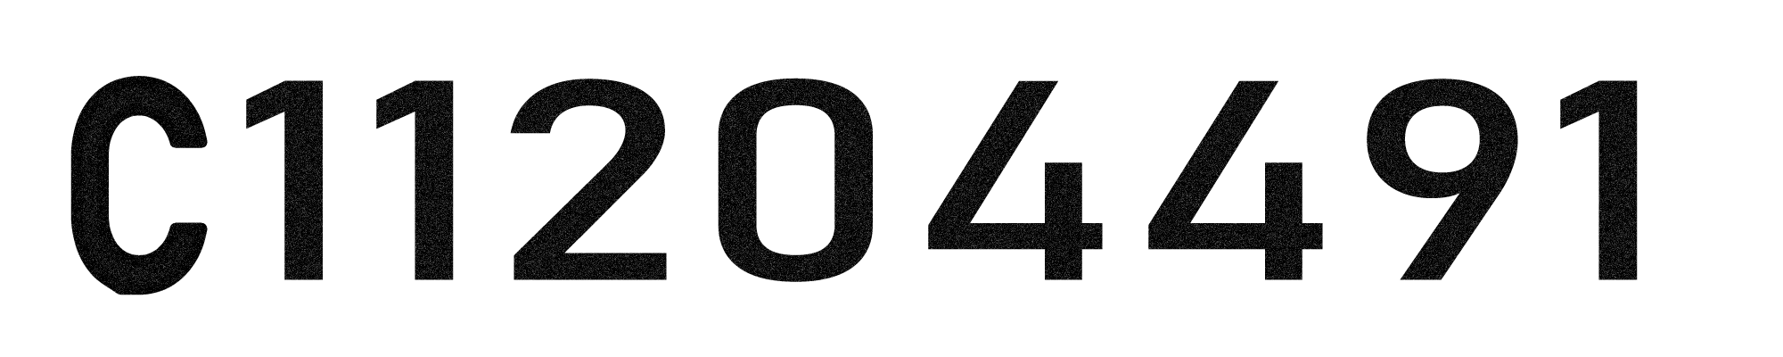
mcad/gbc/decal numero.png
