esp-cpp/esp-box-emu/mcad/gbc/decal trasera.png

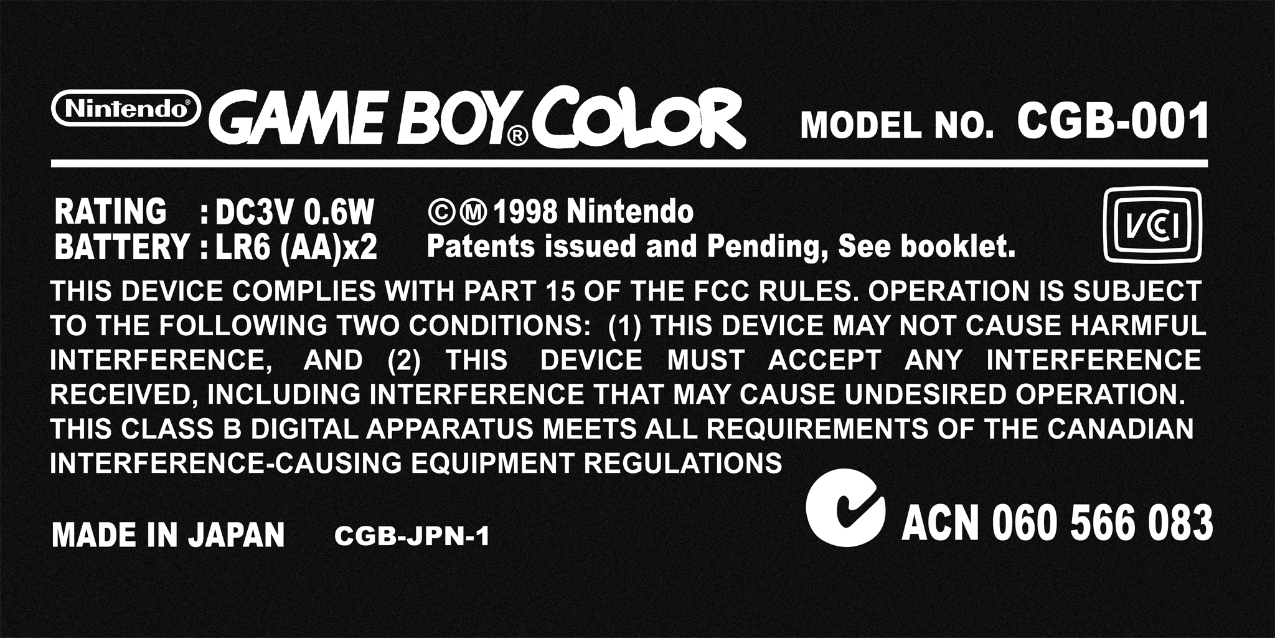
mcad/gbc/decal trasera.png
