esp-cpp/esp-box-emu/mcad/gbc/gbc render final.jpg

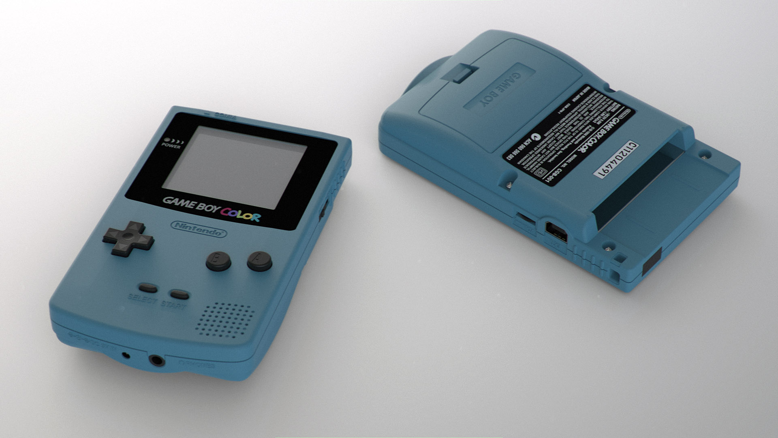
mcad/gbc/gbc render final.jpg
