esp-cpp/esp-box-emu/ecad/elec/src/parts/JST_Sales_America_S2B_PH_SM4_TB_LF__SN/CONN-SMD_P2.00_S2B-PH-SM4-TB-LF-SN.step

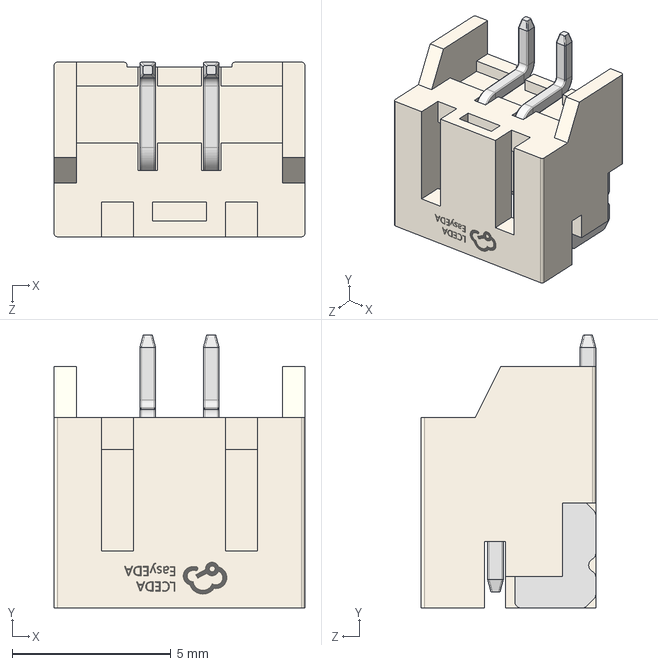
[picture p111: CAD file, 2024-06-29]
ecad/elec/src/parts/JST_Sales_America_S2B_PH_SM4_TB_LF__SN/CONN-SMD_P2.00_S2B-PH-SM4-TB-LF-SN.step
7.90 x 8.60 x 5.50 mm
