esp-cpp/esp-box-emu/ecad/elec/src/parts/JST_Sales_America_SM04B_SRSS_TB_LF__SN/CONN-SMD_SR1.00-WS-4P.step

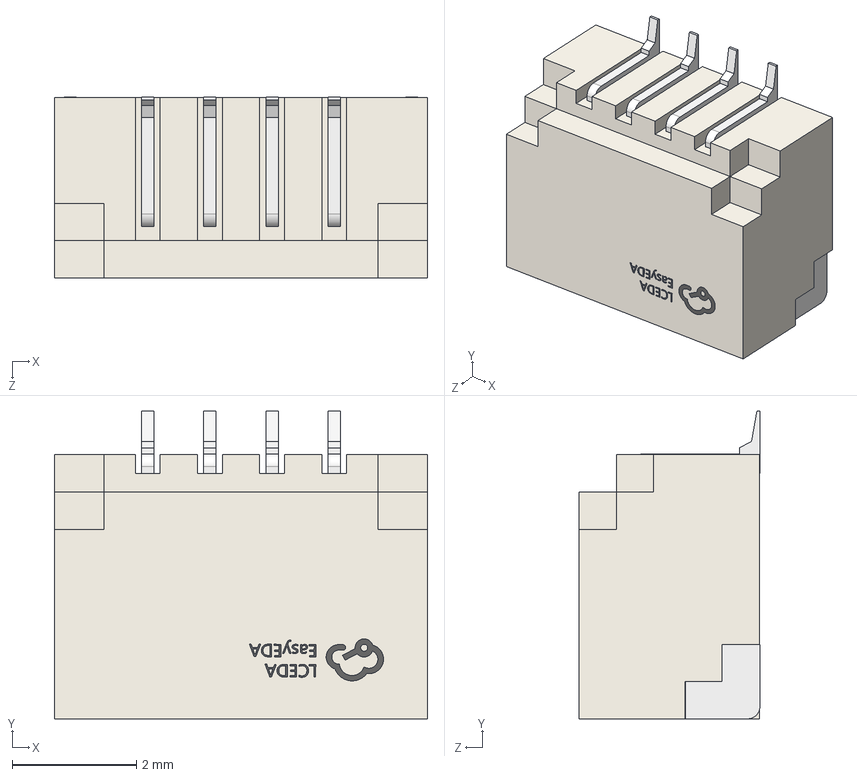
[picture p112: CAD file, 2024-06-29]
ecad/elec/src/parts/JST_Sales_America_SM04B_SRSS_TB_LF__SN/CONN-SMD_SR1.00-WS-4P.step
6.00 x 4.95 x 2.91 mm
