esp-cpp/esp-box-emu/ecad/elec/src/parts/Maxim_Integrated_MAX17048G_T10/TDFN-8_L2.0-W2.0-P0.50-BL-EP1.2.STEP

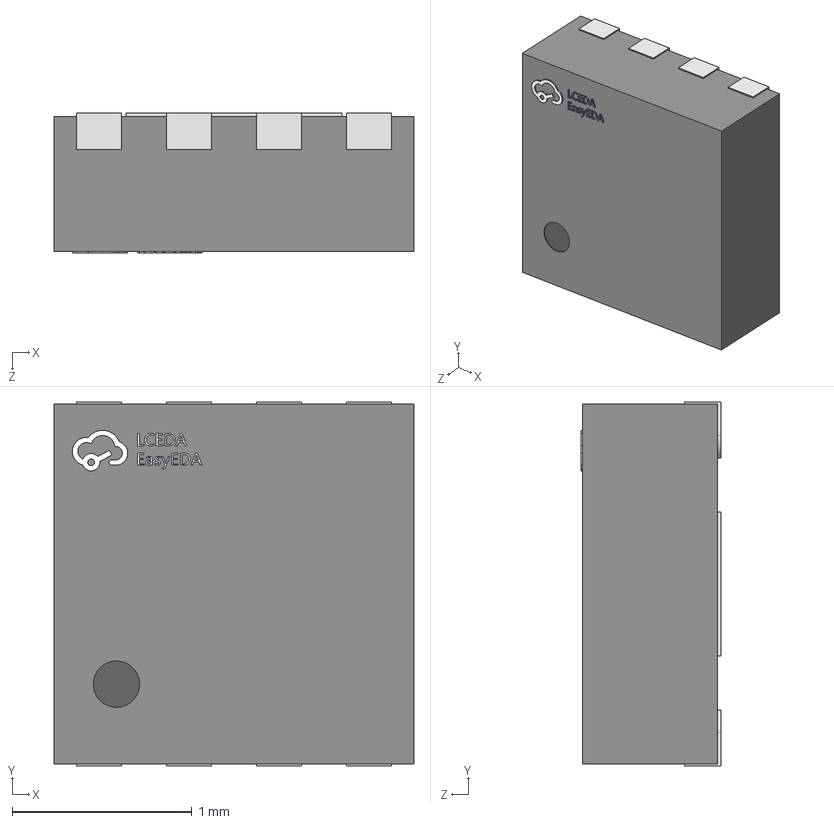
[picture p113: CAD file, 2026-10-04]
ecad/elec/src/parts/Maxim_Integrated_MAX17048G_T10/TDFN-8_L2.0-W2.0-P0.50-BL-EP1.2.STEP
2.00 x 2.02 x 0.78 mm
