esp-cpp/esp-box-emu/ecad/elec/src/parts/Microchip_Tech_MCP73831T_2ACI_OT/SOT-23-5_L2.9-W1.6-H1.1-LS2.8-P0.95.step

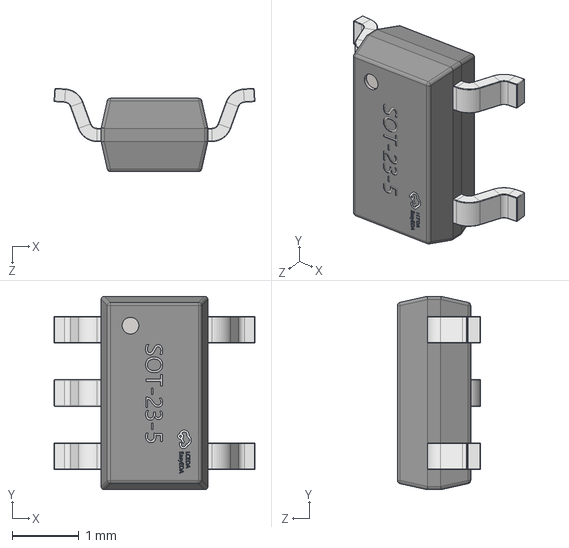
[picture p114: CAD file, 2026-10-04]
ecad/elec/src/parts/Microchip_Tech_MCP73831T_2ACI_OT/SOT-23-5_L2.9-W1.6-H1.1-LS2.8-P0.95.step
3.01 x 2.90 x 1.25 mm
