esp-cpp/esp-box-emu/ecad/elec/src/parts/SHOU_HAN_TS24CA/SW-SMD_2P-TS24CA.STEP

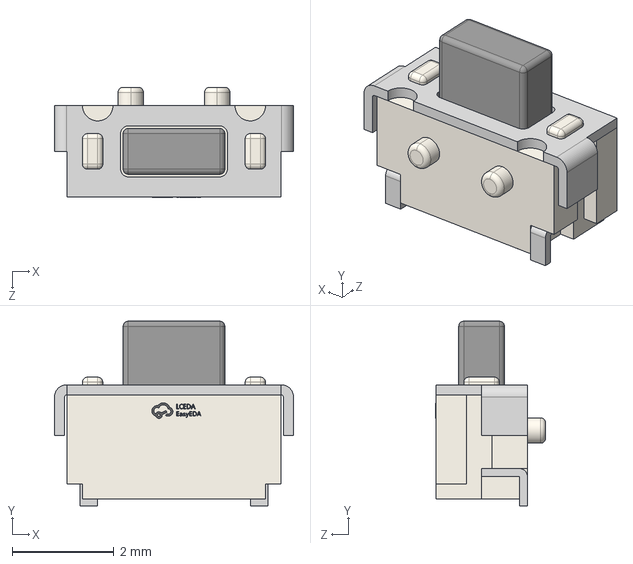
[picture p115: CAD file, 2026-10-04]
ecad/elec/src/parts/SHOU_HAN_TS24CA/SW-SMD_2P-TS24CA.STEP
4.70 x 3.63 x 2.17 mm
