esp-cpp/esp-box-emu/ecad/elec/src/parts/Sunlord_WPN252012H1R5MT/IND-SMD_L2.5-W2.0-H1.2-252012.step

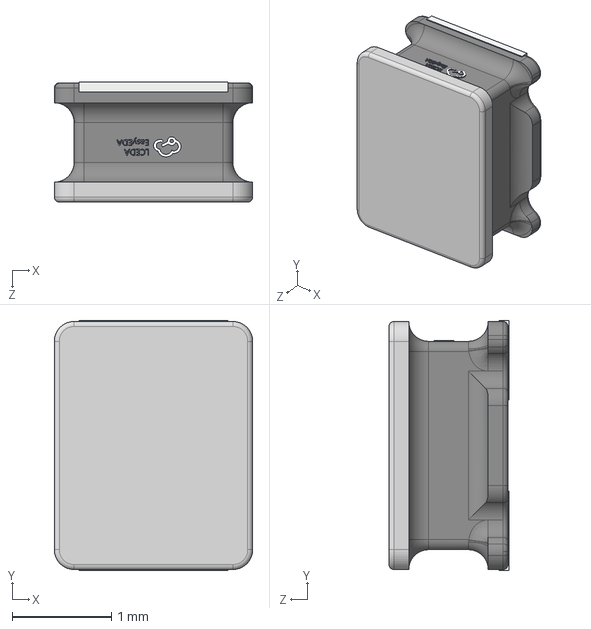
[picture p116: CAD file, 2024-06-29]
ecad/elec/src/parts/Sunlord_WPN252012H1R5MT/IND-SMD_L2.5-W2.0-H1.2-252012.step
2.00 x 2.52 x 1.21 mm
