esp-cpp/esp-box-emu/ecad/elec/src/parts/TE_Connectivity_5_1734857_1/CONN-SMD_5-1734857-1.STEP

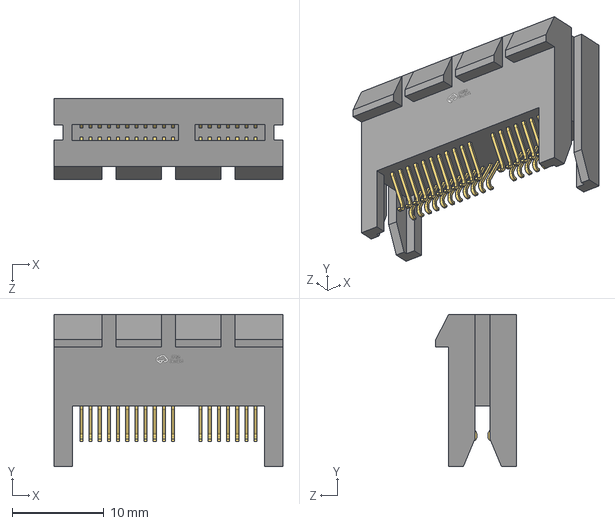
[picture p117: CAD file, 2026-10-04]
ecad/elec/src/parts/TE_Connectivity_5_1734857_1/CONN-SMD_5-1734857-1.STEP
25.0 x 16.6 x 8.80 mm
