esp-cpp/esp-box-emu/ecad/elec/src/parts/Texas_Instruments_DRV2605LDGSR/VSSOP-10_L3.0-W3.0-H1.1-LS4.9-P0.50.step

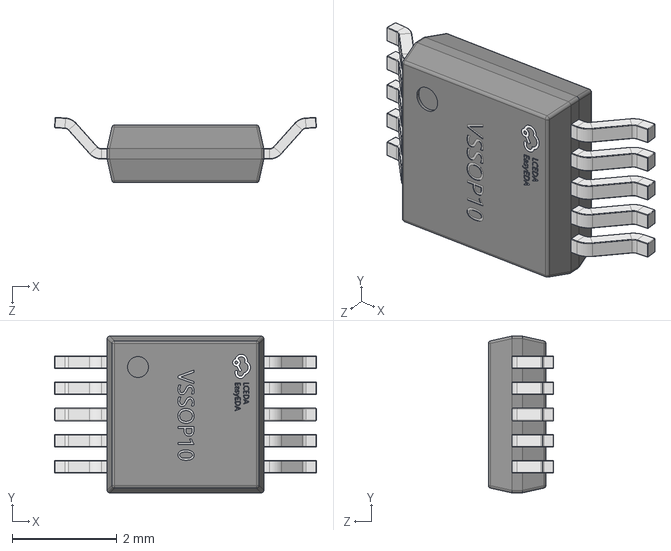
[picture p118: CAD file, 2024-06-29]
ecad/elec/src/parts/Texas_Instruments_DRV2605LDGSR/VSSOP-10_L3.0-W3.0-H1.1-LS4.9-P0.50.step
5.01 x 3.00 x 1.25 mm
