esp-cpp/esp-box-emu/ecad/elec/src/parts/Yongyu_Photoelectric_SZYY0805R/LED0805-RD.step

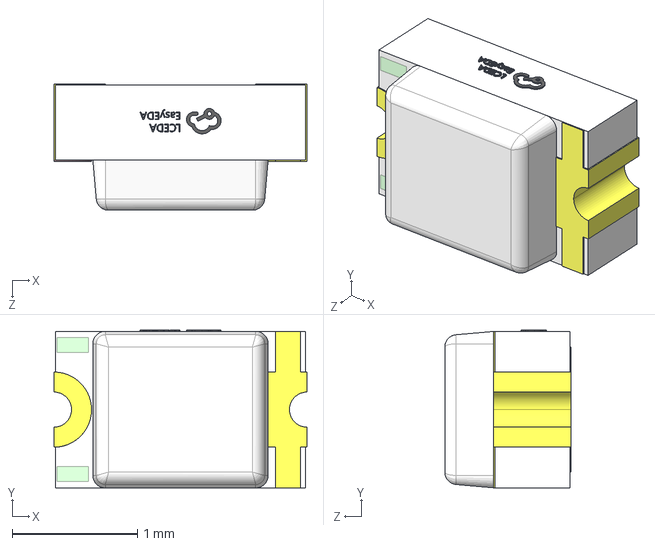
[picture p119: CAD file, 2026-10-04]
ecad/elec/src/parts/Yongyu_Photoelectric_SZYY0805R/LED0805-RD.step
2.02 x 1.26 x 1.01 mm
