esp-cpp/esp-box-emu/ecad/elec/src/parts/Yuandi_TYPE_611_T3_W/USB-C-SMD_TYPE-611-T3-W.step

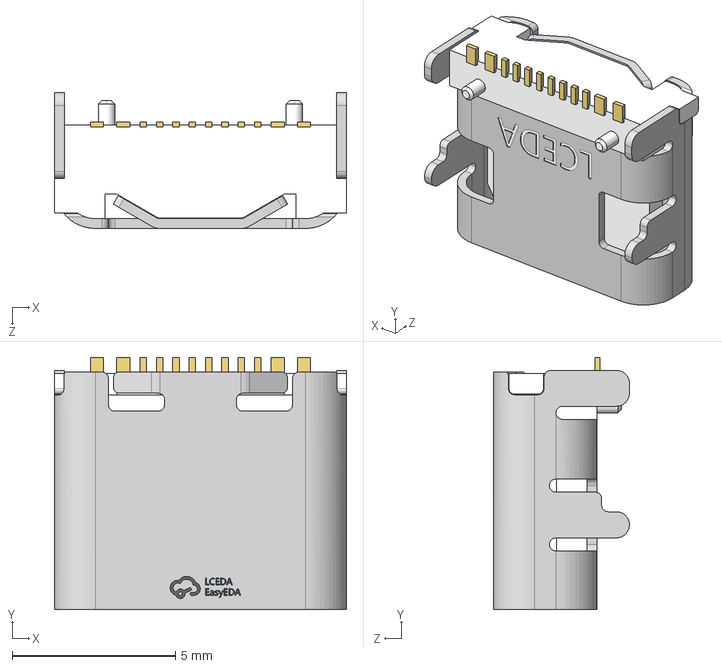
[picture p120: CAD file, 2026-10-04]
ecad/elec/src/parts/Yuandi_TYPE_611_T3_W/USB-C-SMD_TYPE-611-T3-W.step
8.94 x 7.73 x 4.16 mm
