esp-cpp/esp-box-emu/mcad/box/ESP32-S3-BOX-BOTTOM-V2_20211214.STEP

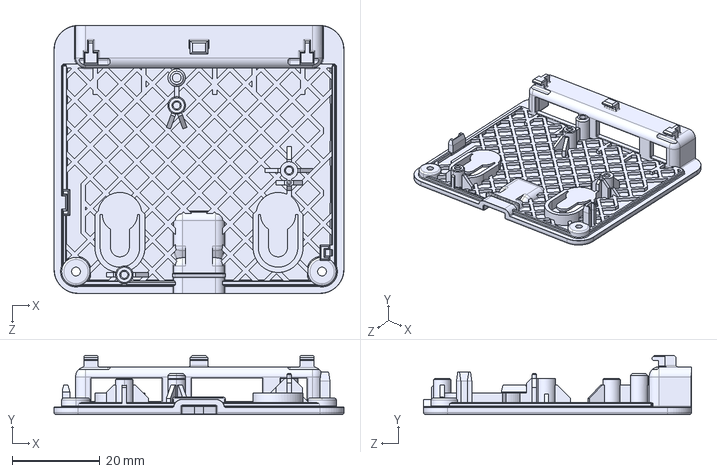
[picture p121: CAD file, 2023-01-02]
mcad/box/ESP32-S3-BOX-BOTTOM-V2_20211214.STEP
66.0 x 13.5 x 61.0 mm
