esp-cpp/esp-box-emu/mcad/esp-box-emu-3-pcb.dxf

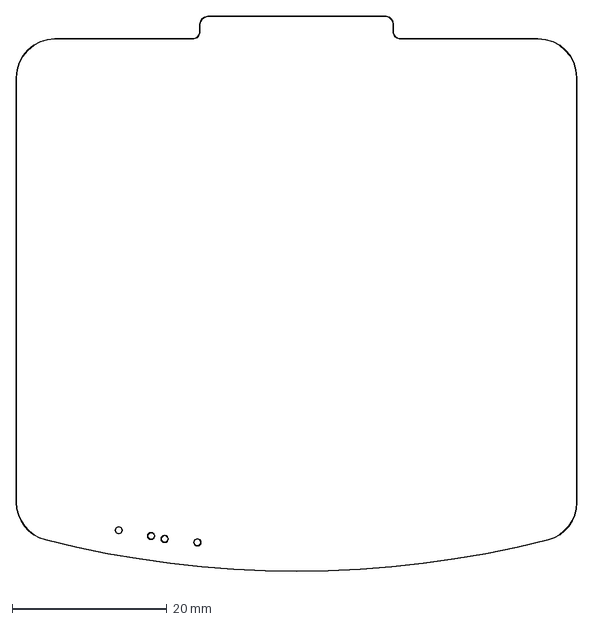
[picture p122: CAD file, 2024-06-29]
mcad/esp-box-emu-3-pcb.dxf
72.5 x 73.1 mm
