esp-cpp/esp-box-emu/mcad/box/ESP32-S3-BOX-TOP-V2_20211215A.STEP

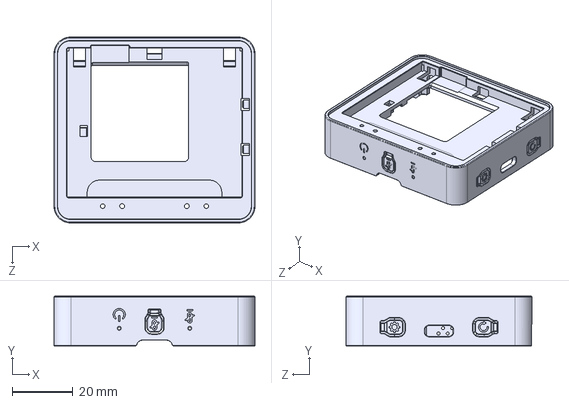
[picture p123: CAD file, 2023-01-02]
mcad/box/ESP32-S3-BOX-TOP-V2_20211215A.STEP
66.0 x 16.3 x 61.0 mm
