esp-cpp/esp-box-emu/mcad/esp-box-emu-pcb.dxf

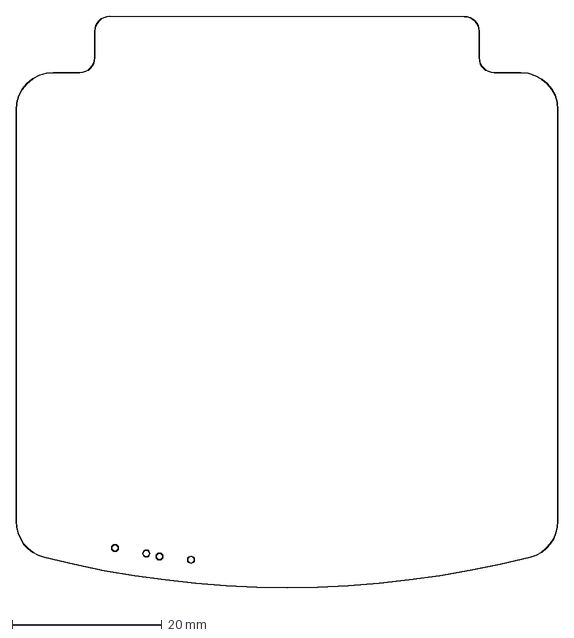
[picture p124: CAD file, 2024-06-29]
mcad/esp-box-emu-pcb.dxf
72.5 x 77.7 mm
