esp-cpp/esp-box-emu/mcad/box/1_DOCK_20211011.STEP

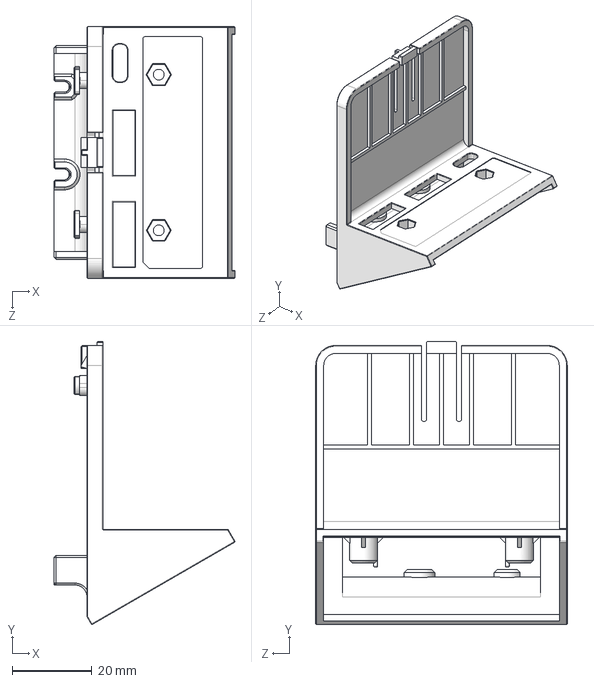
[picture p125: CAD file, 2023-01-02]
mcad/box/1_DOCK_20211011.STEP
45.3 x 70.9 x 63.0 mm
