esp-cpp/esp-box-emu/mcad/gbc_a_b v11.stl

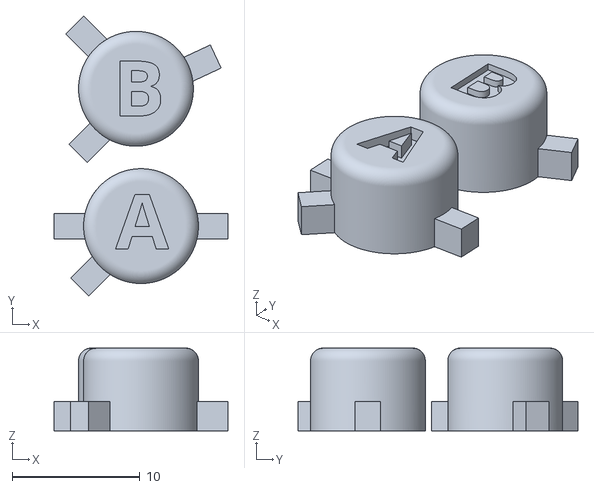
[picture p126: CAD file, 2024-01-21]
mcad/gbc_a_b v11.stl
13.6 x 21.9 x 6.50
