esp-cpp/esp-box-emu/mcad/Box Emu 3 Top.stl

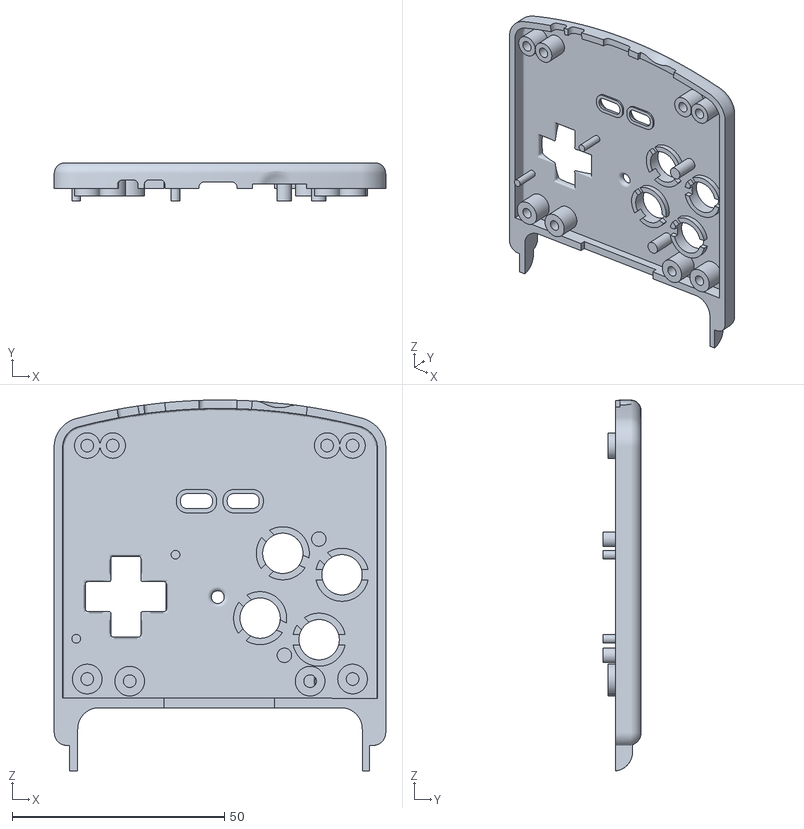
[picture p127: CAD file, 2024-01-21]
mcad/Box Emu 3 Top.stl
78.1 x 9.00 x 87.4
