esp-cpp/esp-box-emu/mcad/Box Emu Top.stl

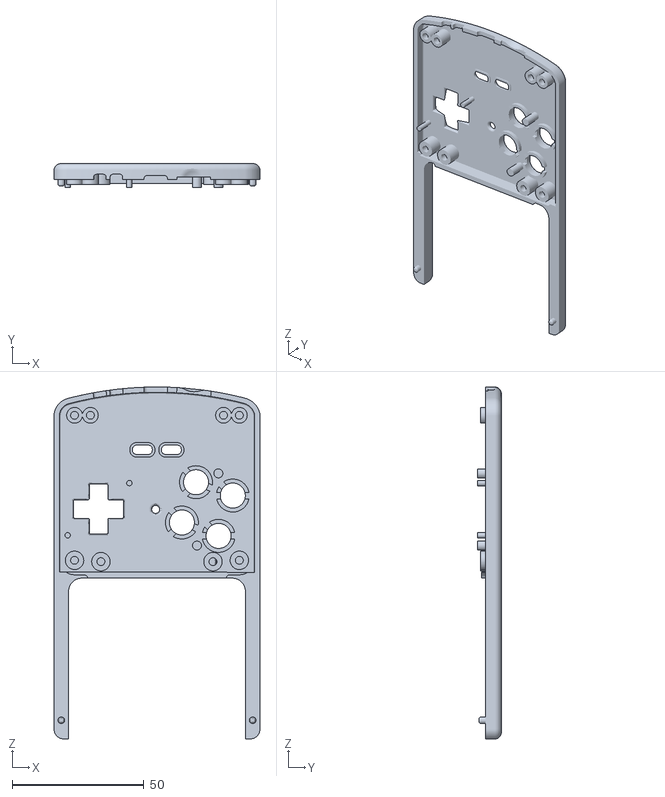
[picture p128: CAD file, 2024-01-21]
mcad/Box Emu Top.stl
78.1 x 9.00 x 133.5
