esp-cpp/esp-box-emu/mcad/Translucent Light Pipe v2.stl

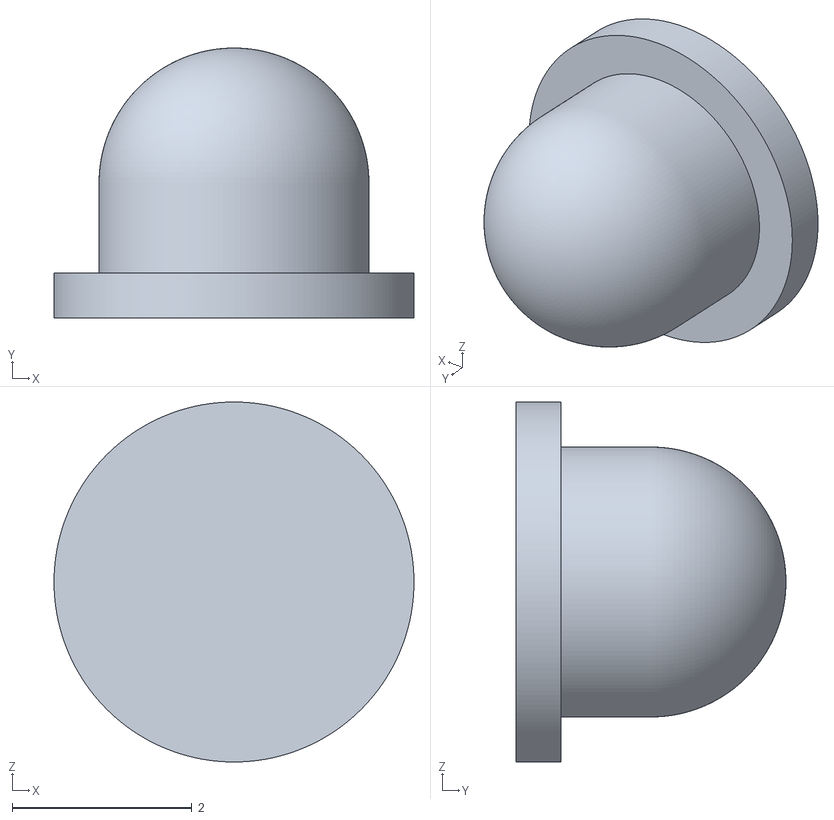
[picture p129: CAD file, 2023-12-18]
mcad/Translucent Light Pipe v2.stl
4.00 x 3.00 x 4.00
