esp-cpp/esp-box-emu/mcad/Box Emu Bottom.stl

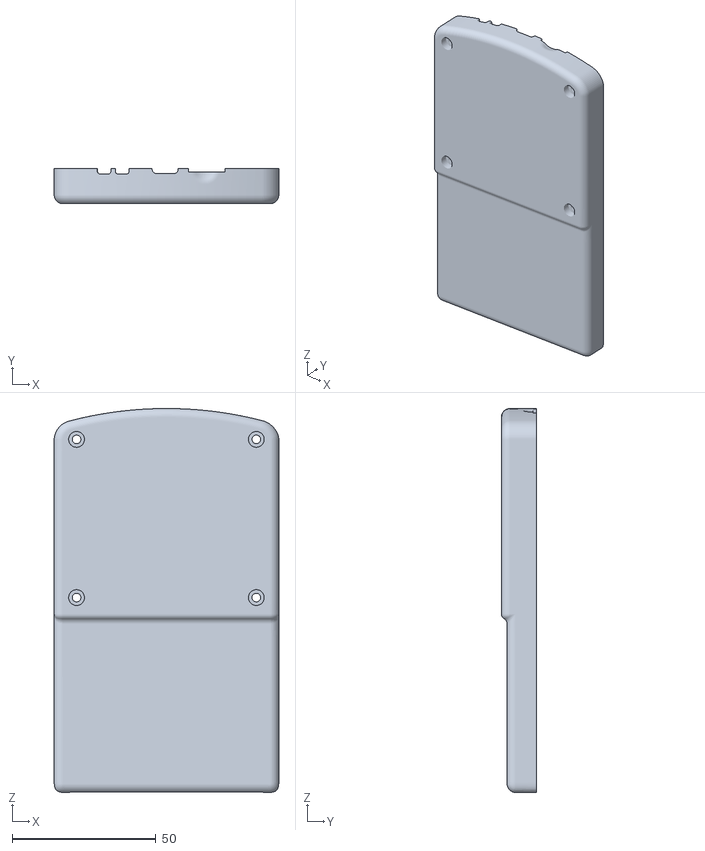
[picture p130: CAD file, 2023-12-18]
mcad/Box Emu Bottom.stl
78.1 x 12.3 x 133.5
