esp-cpp/esp-box-emu/mcad/Box Emu 3 Bottom.stl

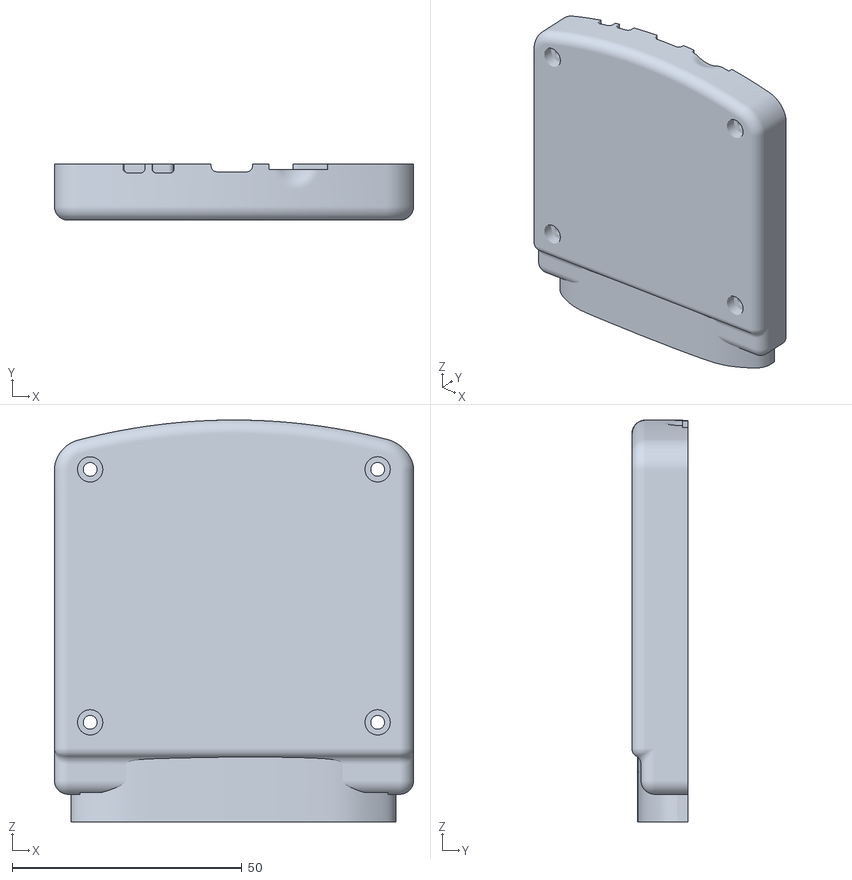
[picture p131: CAD file, 2023-12-18]
mcad/Box Emu 3 Bottom.stl
78.1 x 12.3 x 87.4
