esp-cpp/esp-box-emu/mcad/gbc_d_pad v7.stl

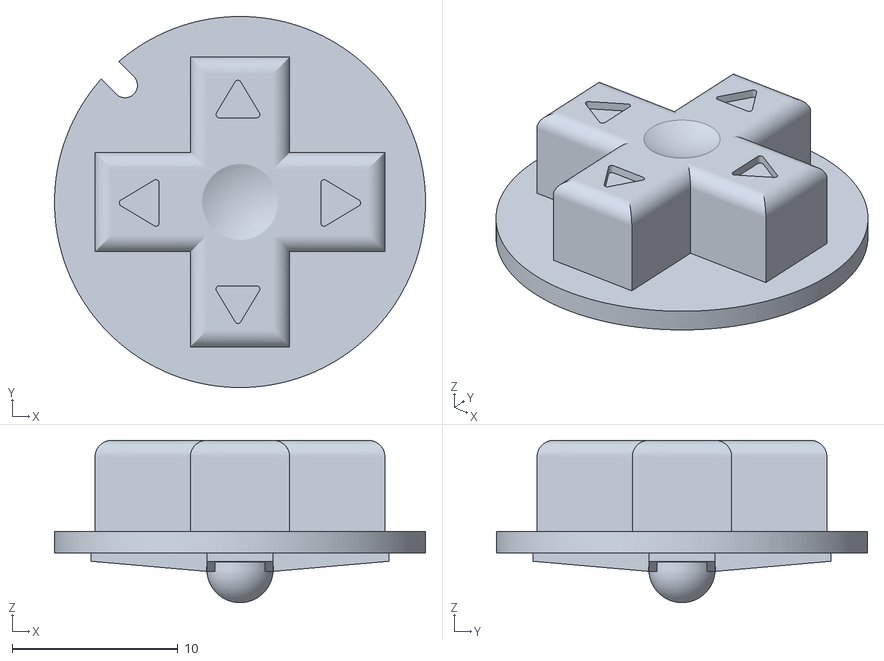
[picture p132: CAD file, 2023-12-18]
mcad/gbc_d_pad v7.stl
22.4 x 22.4 x 9.80
