esp-cpp/esp-box-emu/mcad/Button Volume Up_Down.stl

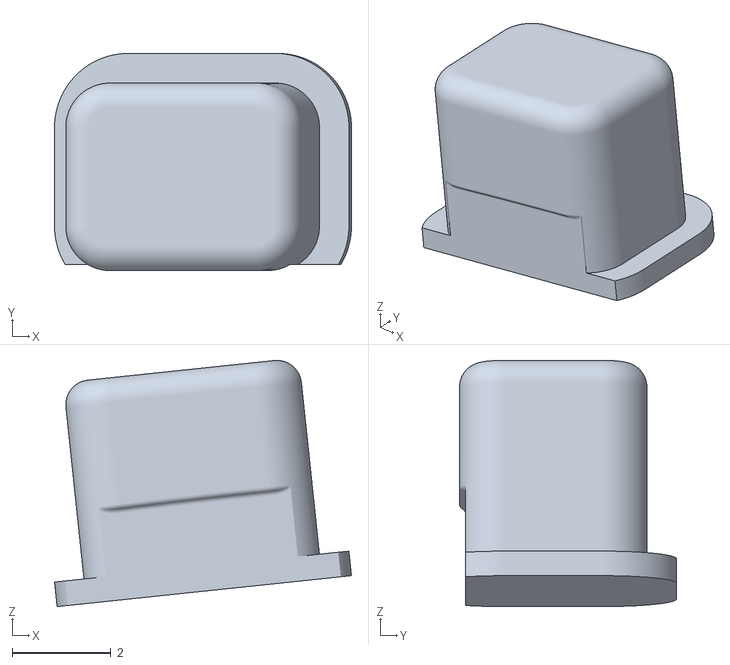
[picture p133: CAD file, 2023-12-18]
mcad/Button Volume Up_Down.stl
6.02 x 4.40 x 4.99
