esp-cpp/esp-box-emu/images/esp-box-emu housing and assembly v160.png

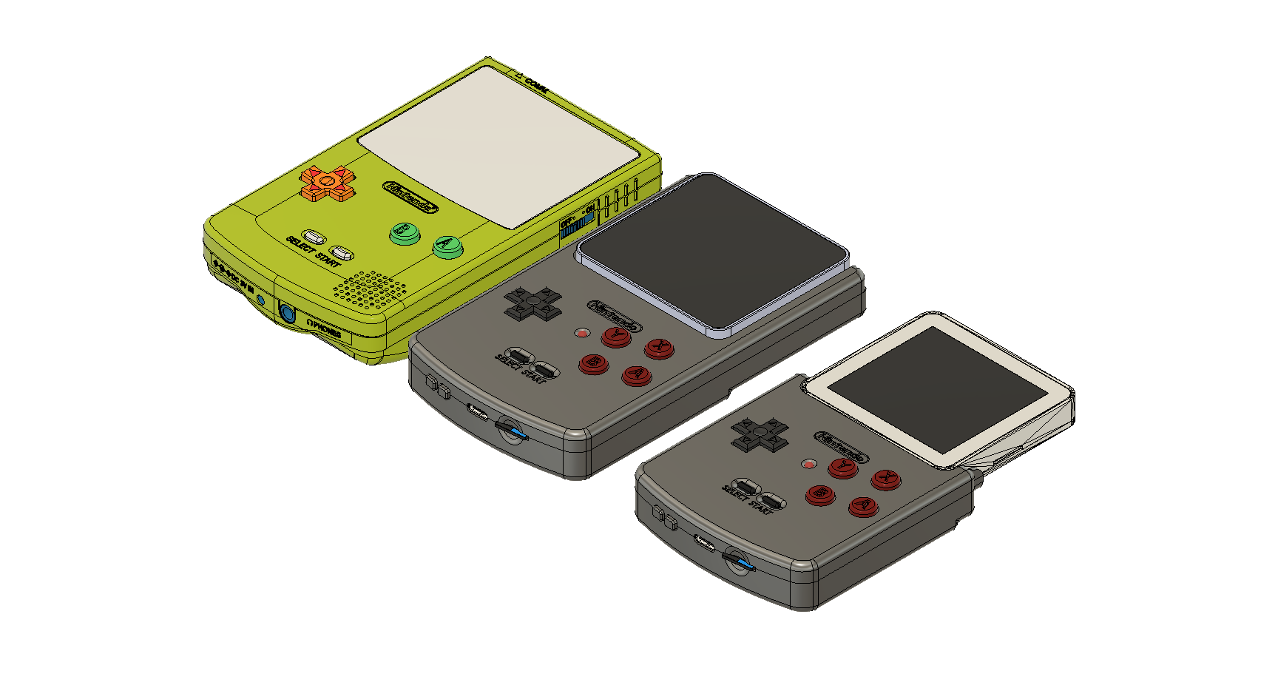
images/esp-box-emu housing and assembly v160.png
