esp-cpp/esp-box-emu/mcad/gbc/gbc prueba.jpg

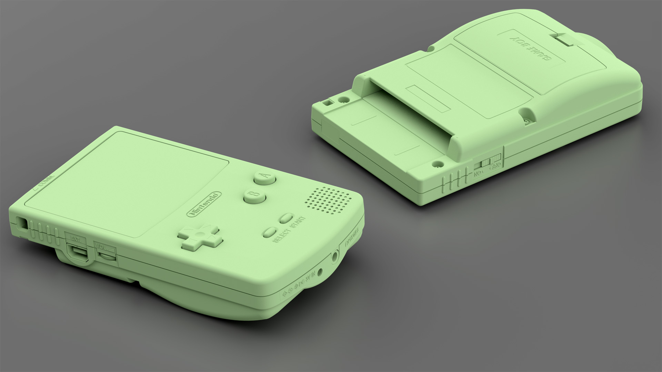
mcad/gbc/gbc prueba.jpg
