esp-cpp/esp-box-emu/ecad/elec/src/parts/Yuandi_TYPE_611_T3_W/Yuandi-TYPE-611-T3-W_C2689844.pdf

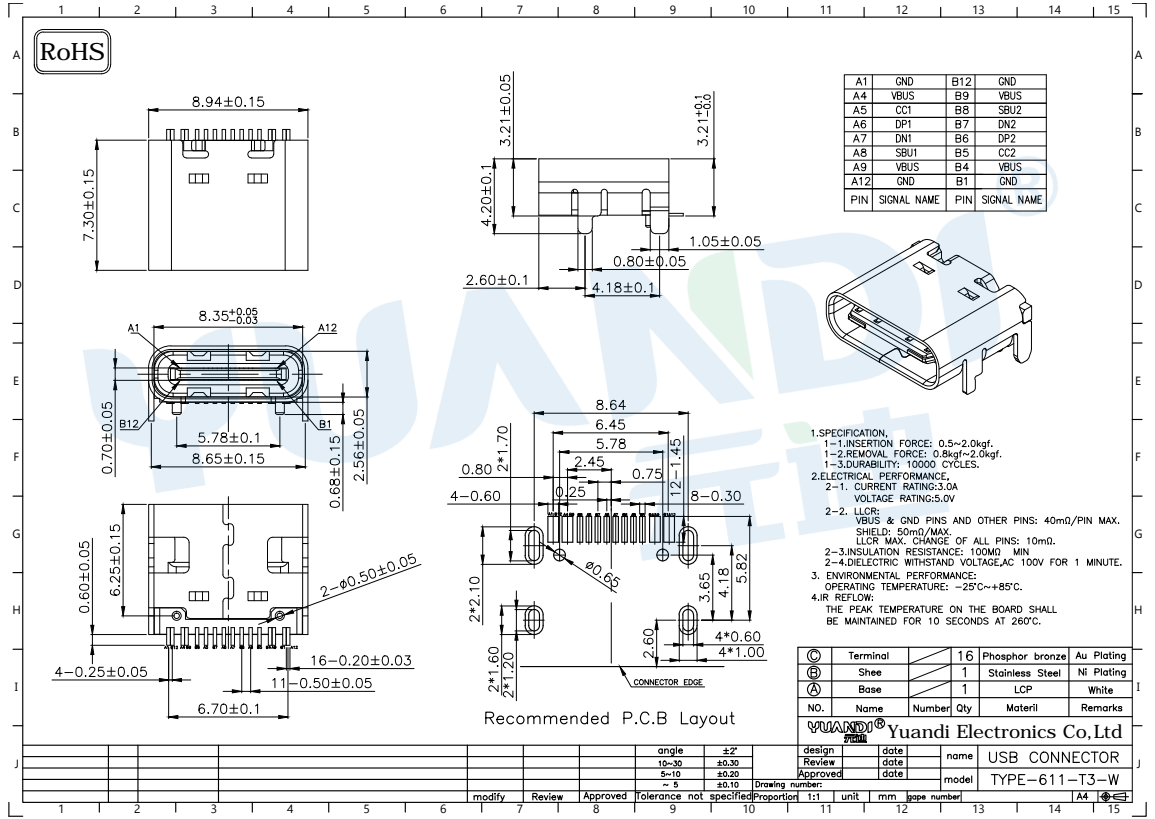
[picture p144: page 1]
G ABCDEFGHIJ; IADFHJ Yuandi Electronics Co,Ltd RoHS
