esp-cpp/esp-box-emu/ecad/.ato/modules/atopile/ti-tps63020/parts/cjiang_FHD4020S_1R0MT/2304140030_cjiang--Changjiang-Microelectronics-Tech-FHD4020S-1R0MT_C602028.pdf

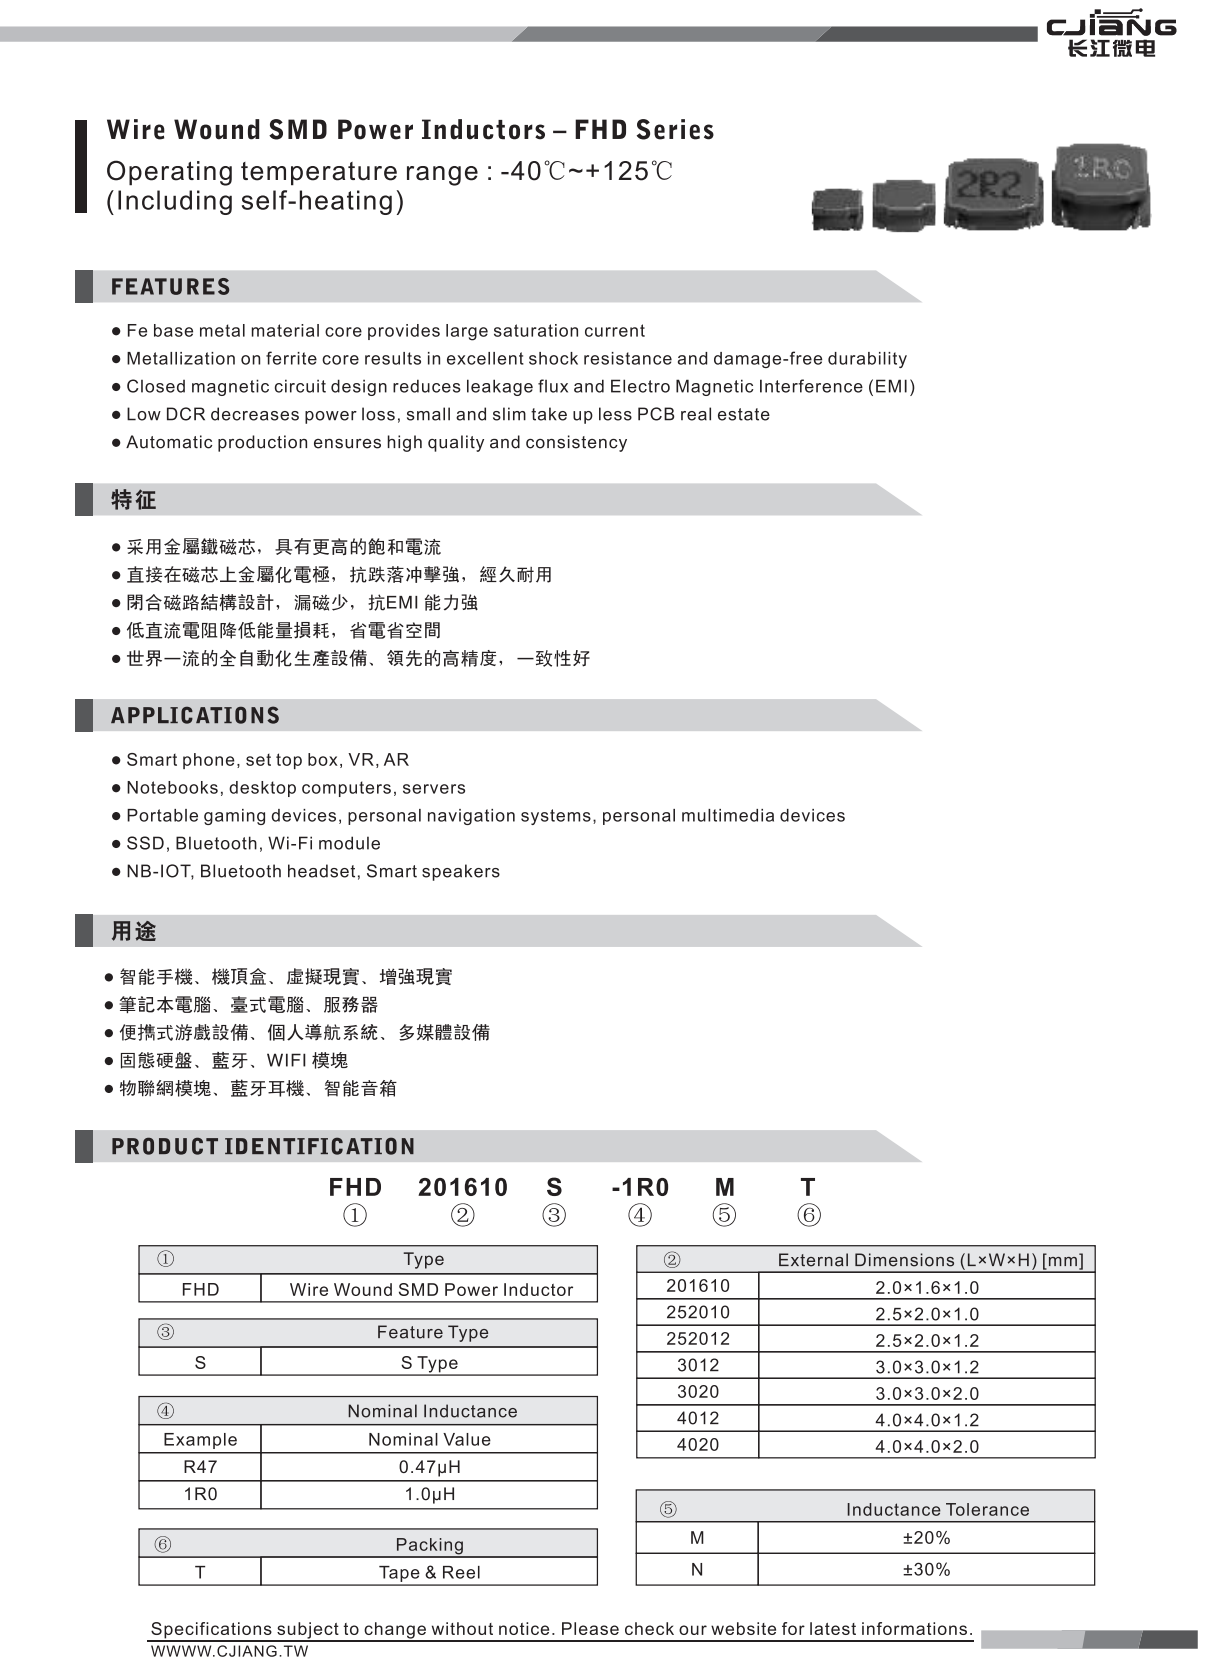
[picture p145: page 1]

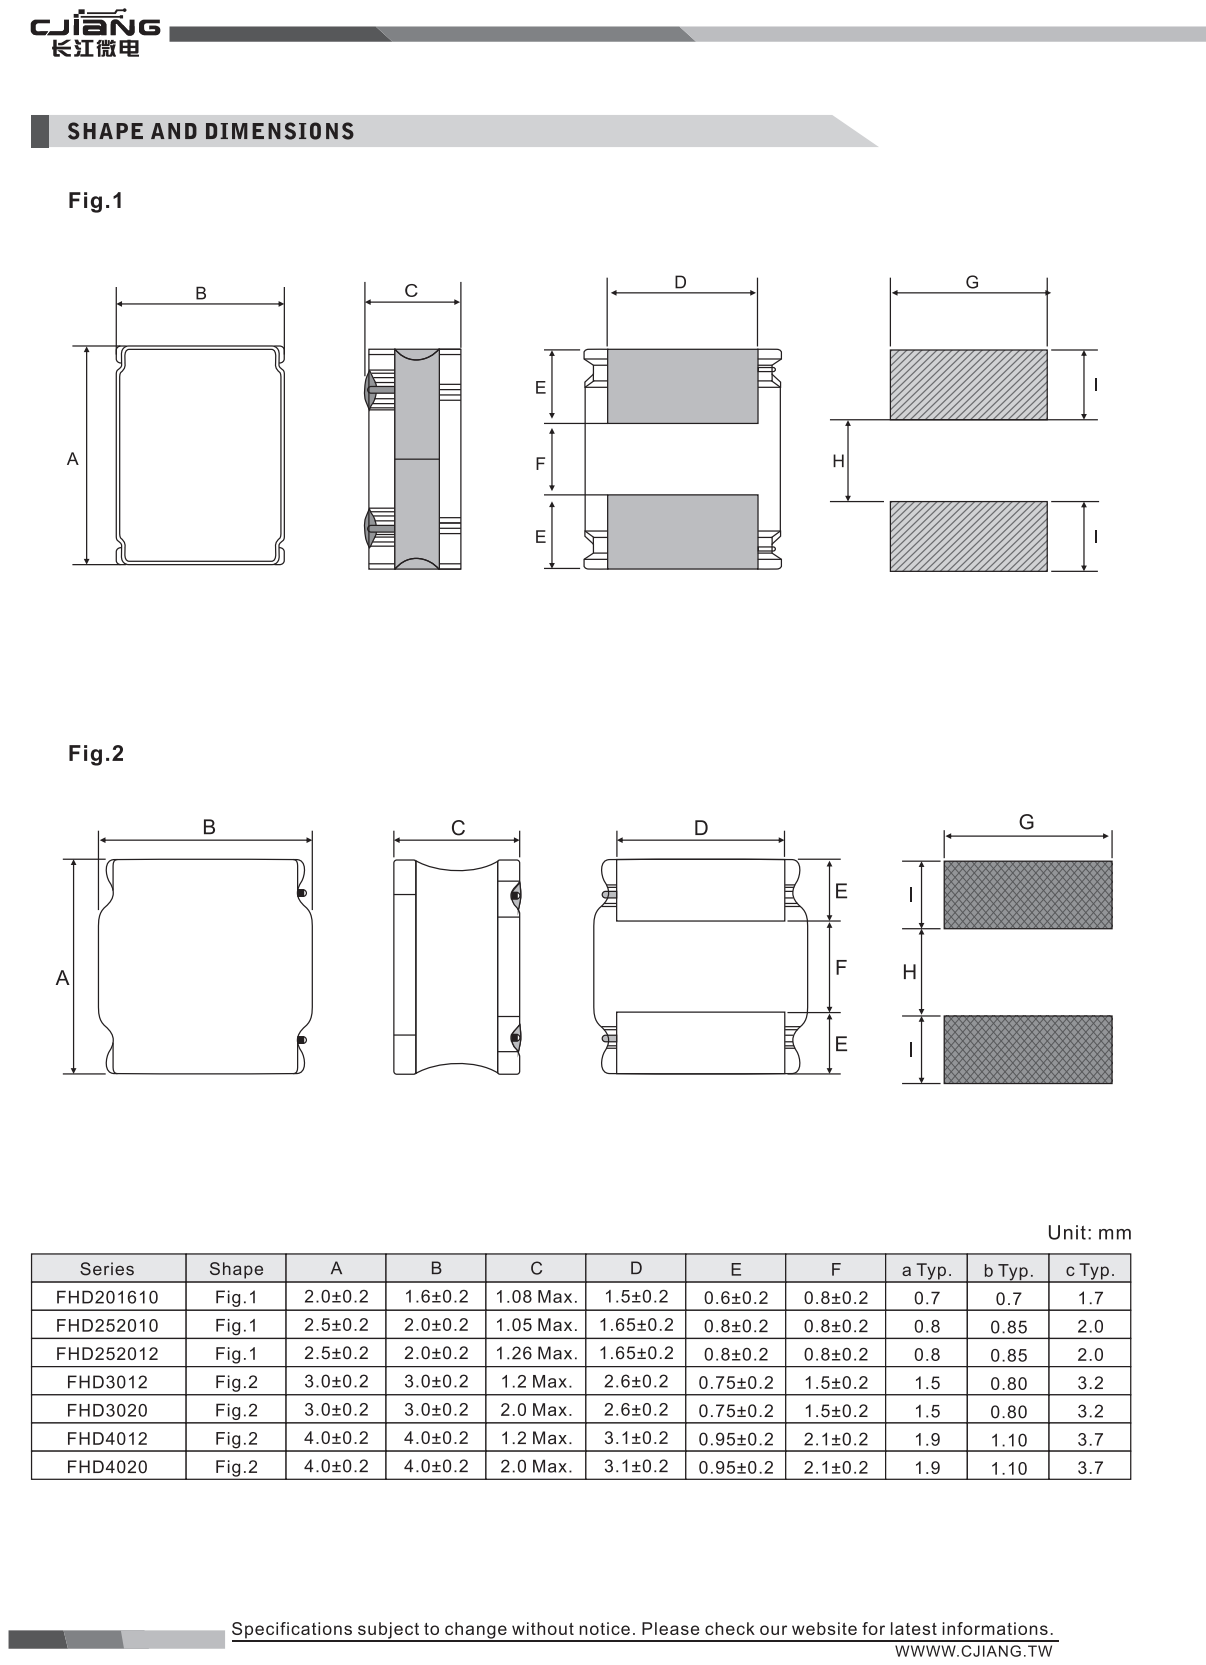
[picture p146: page 2]

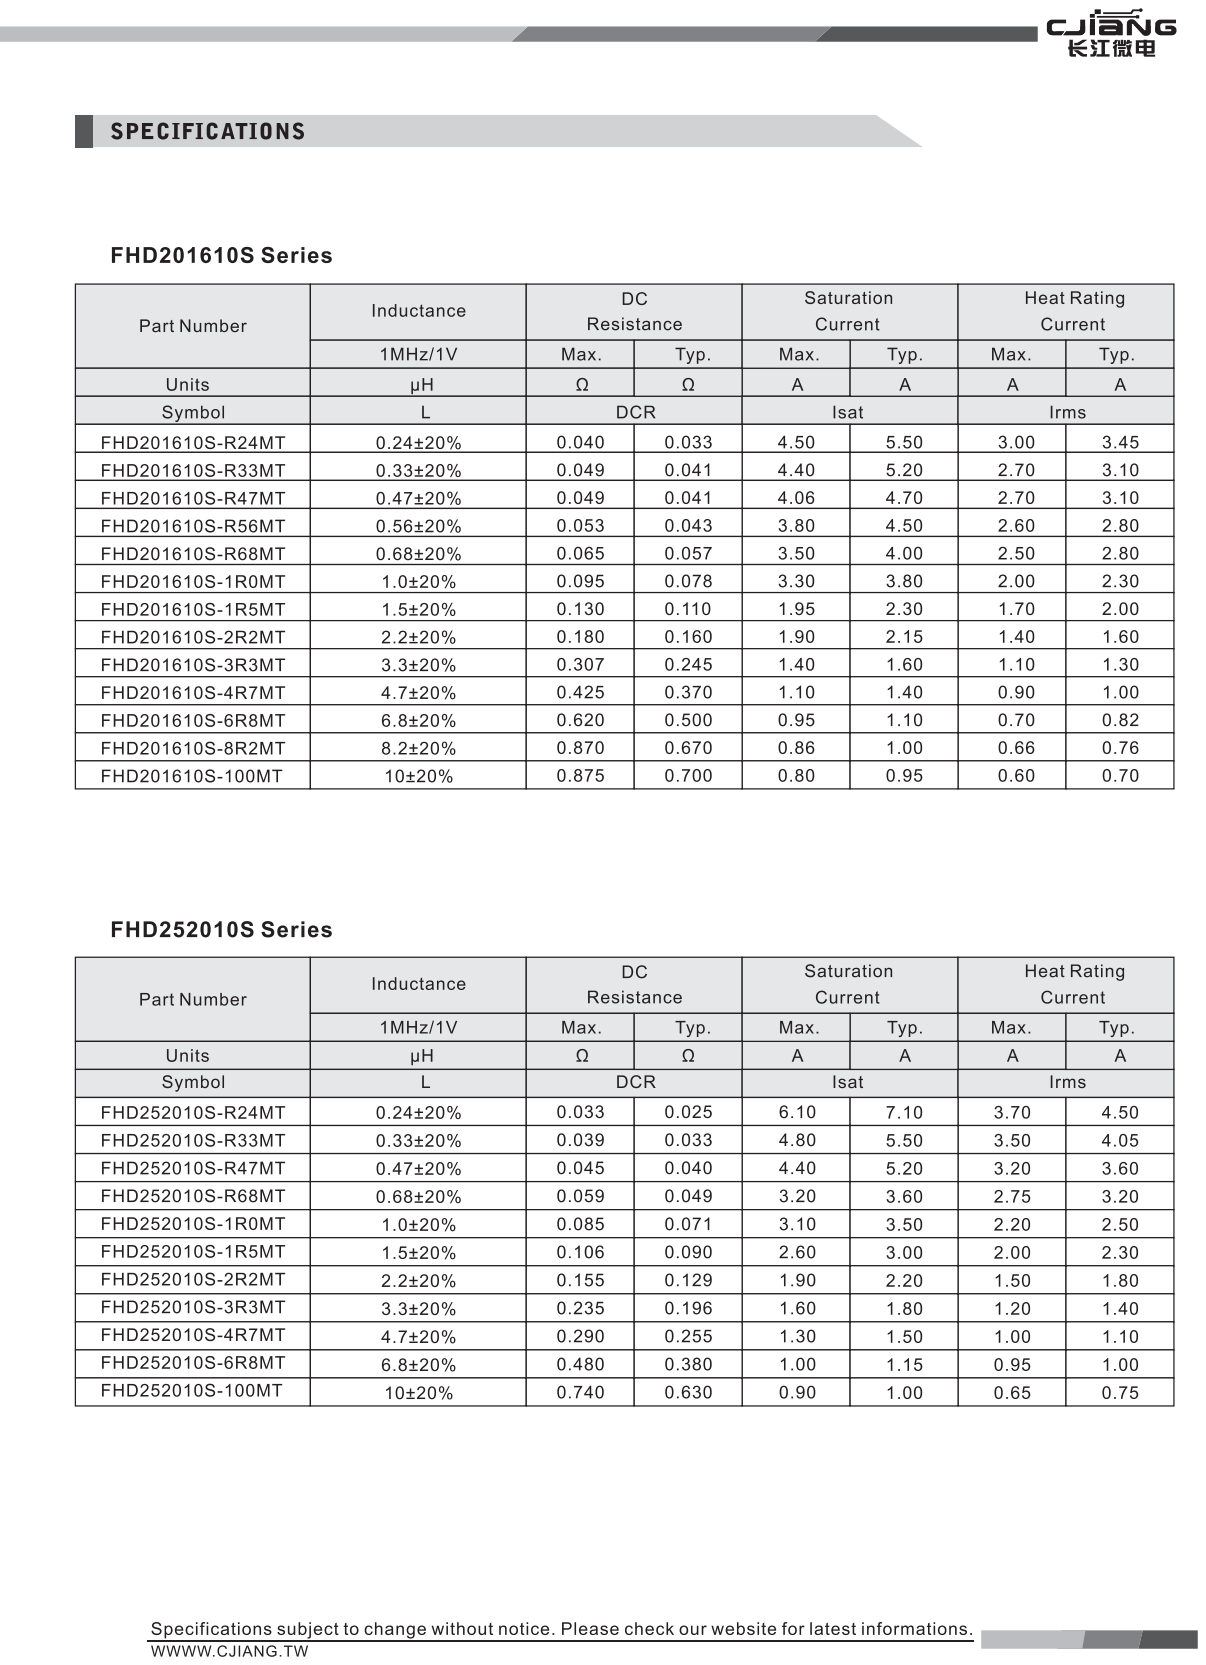
[picture p147: page 3]

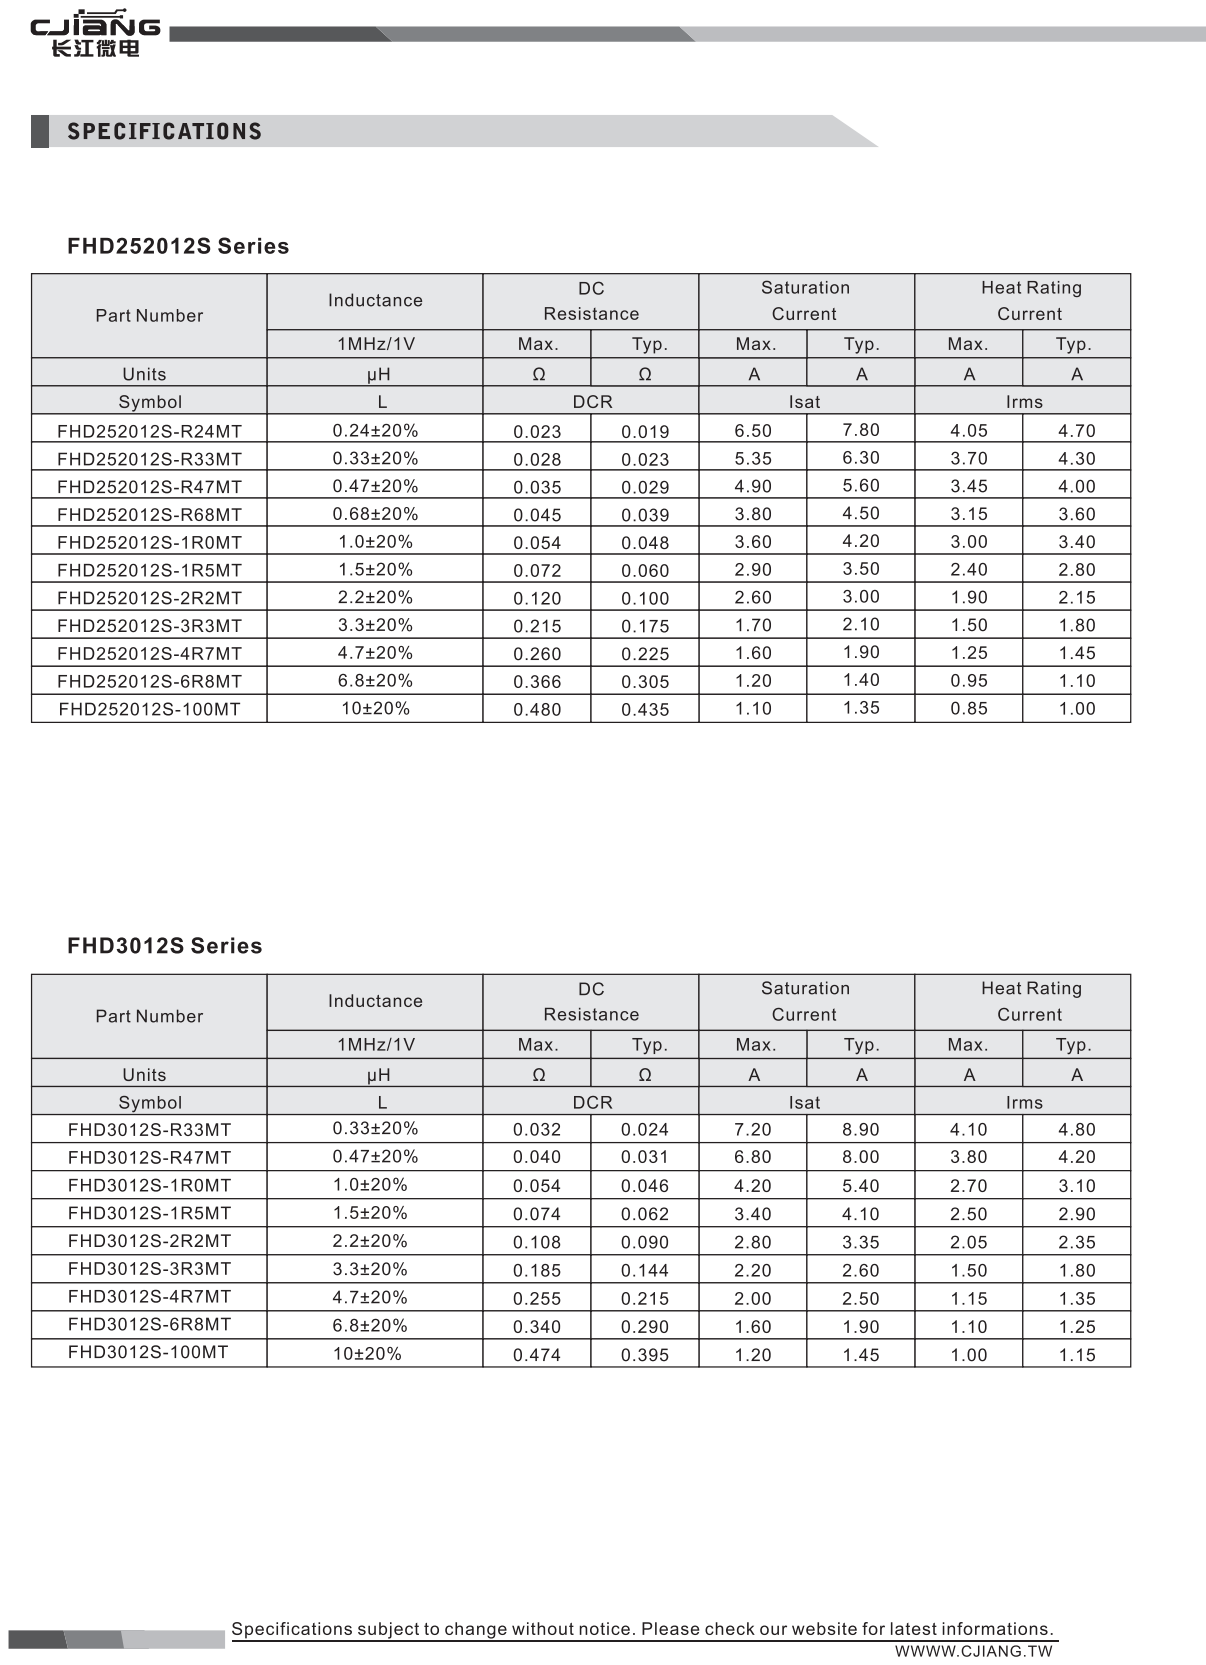
[picture p148: page 4]

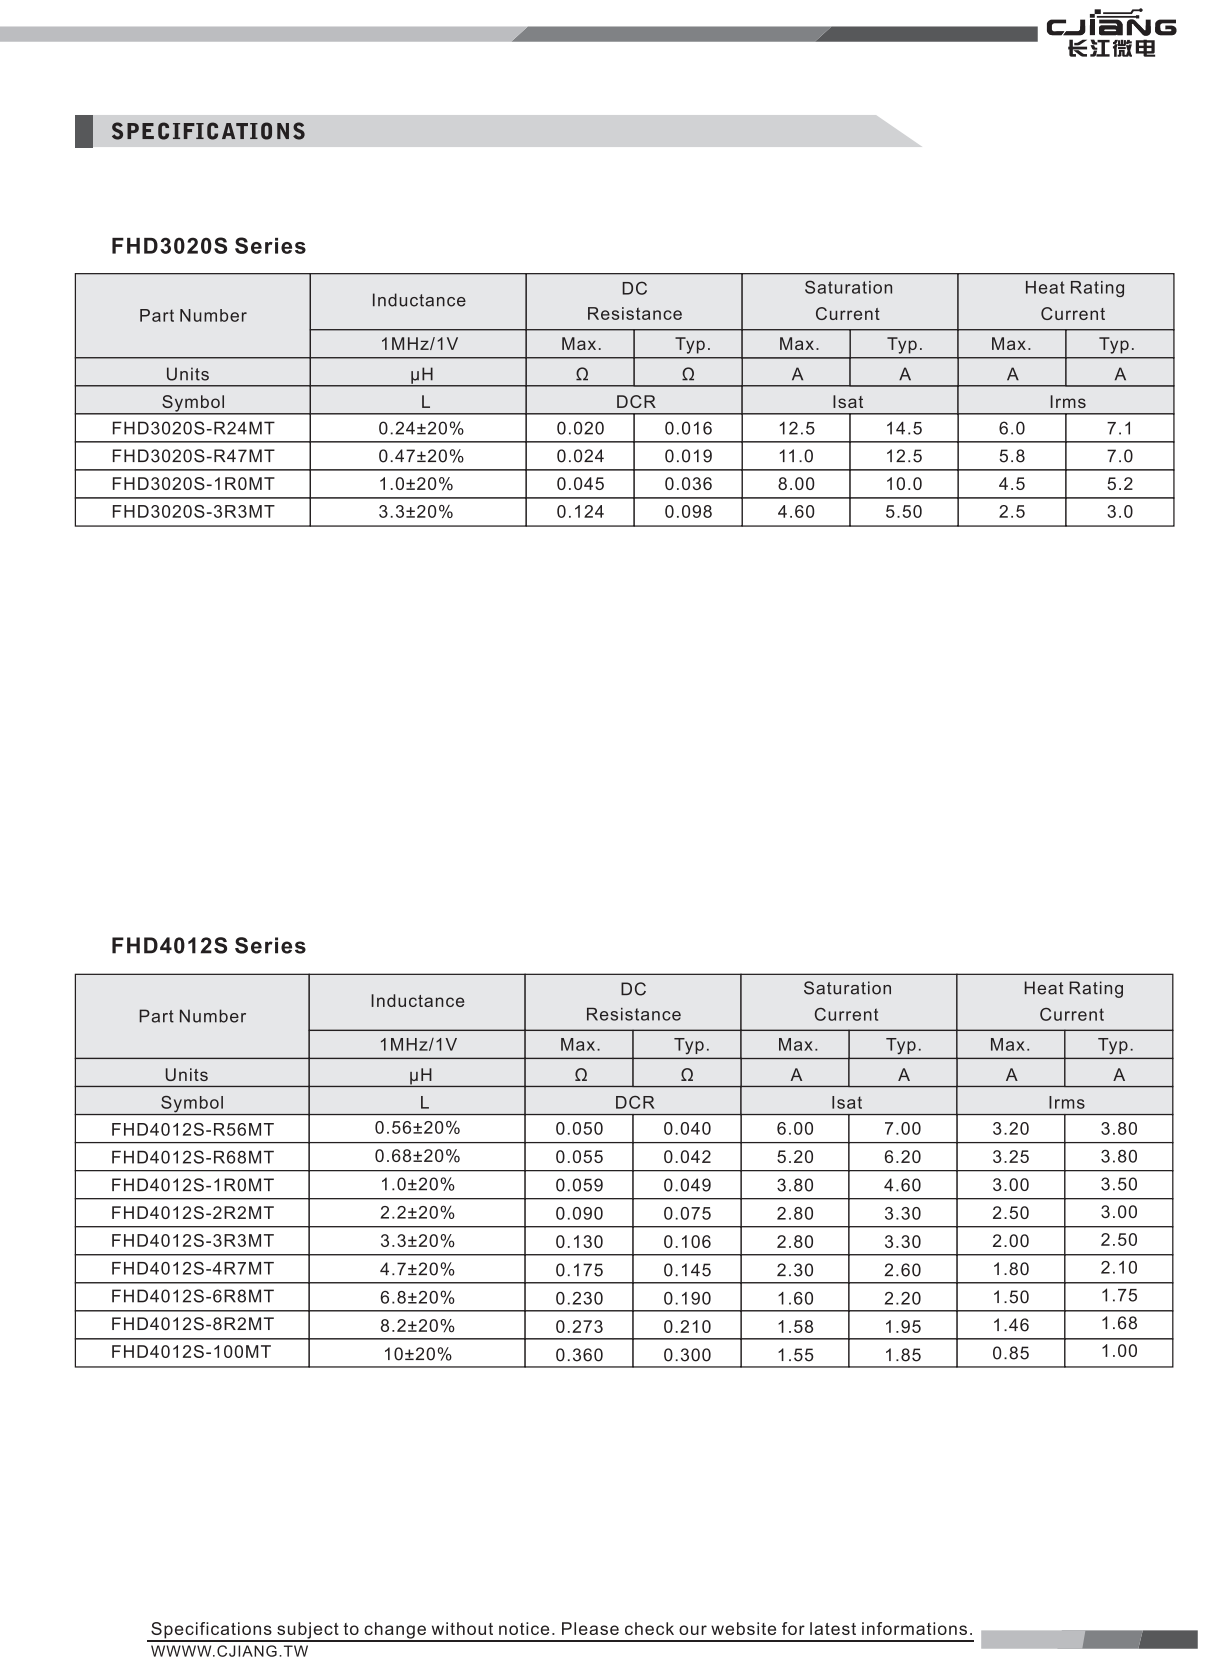
[picture p149: page 5]

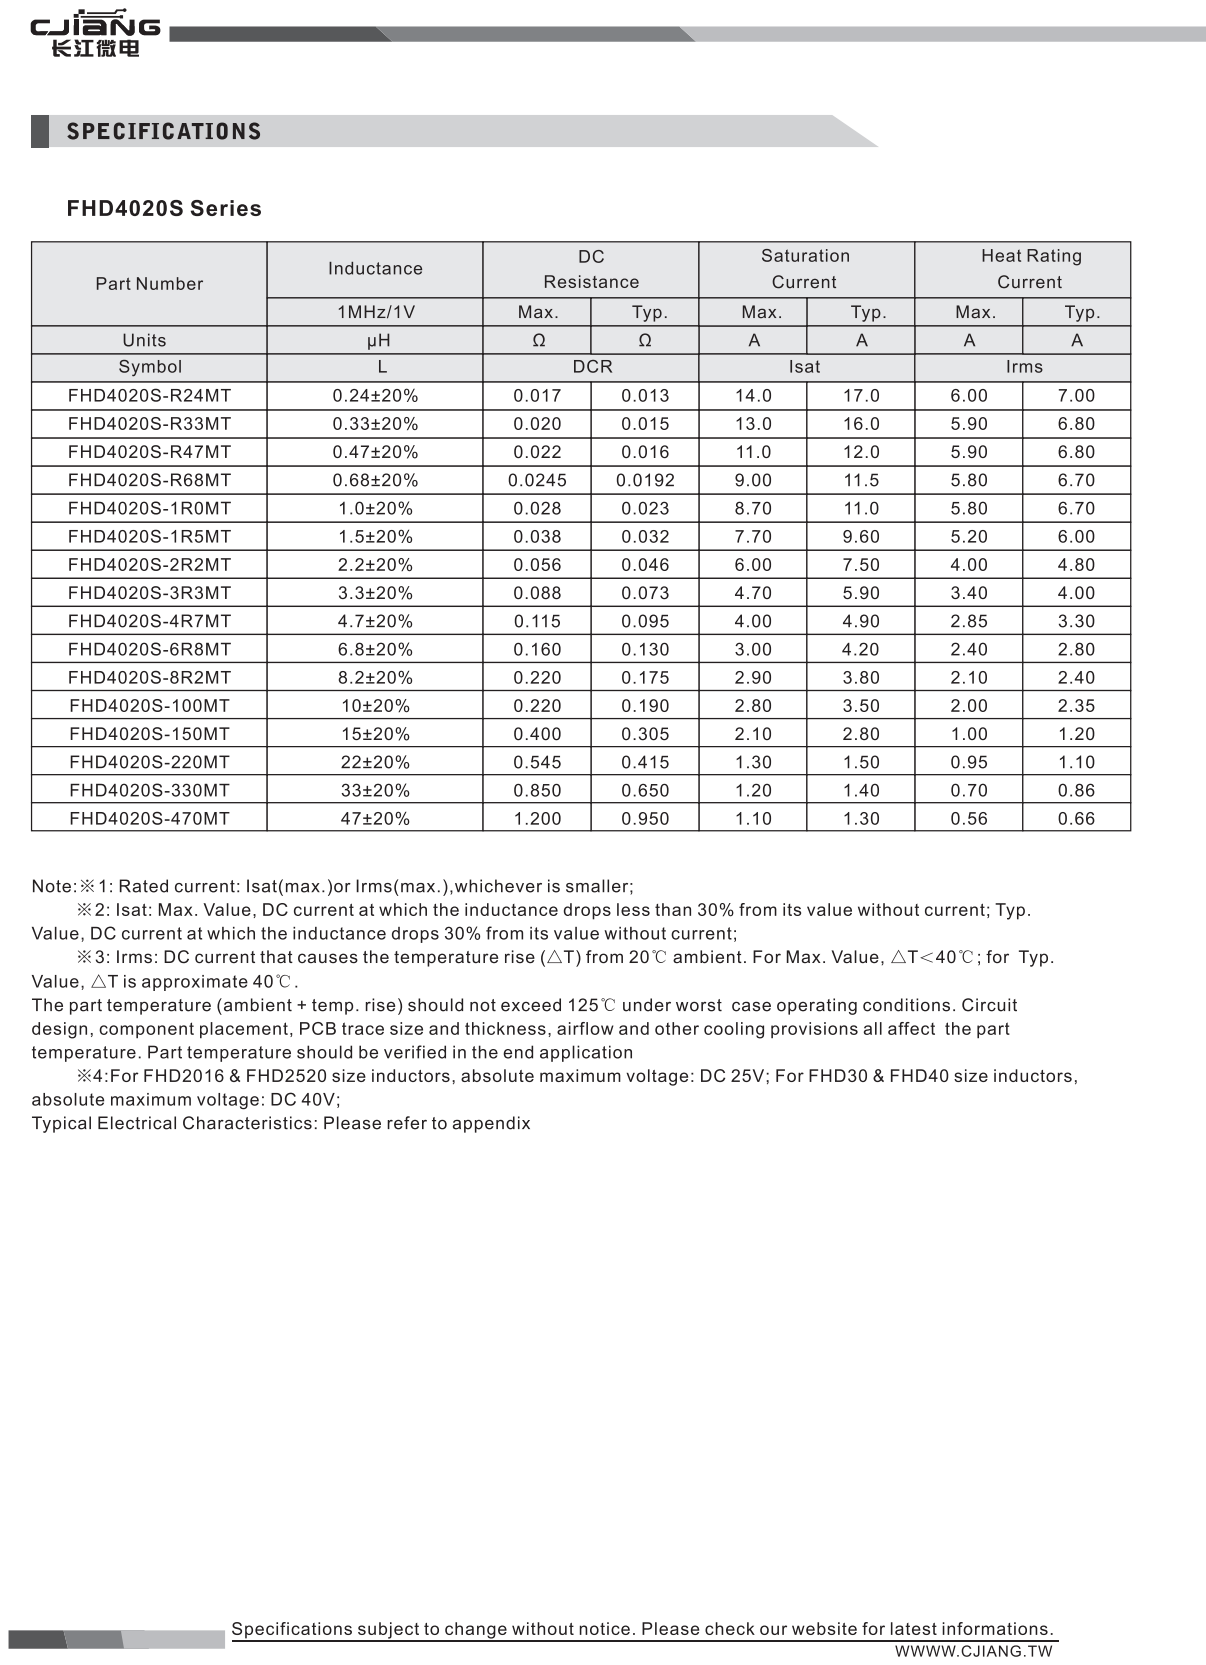
[picture p150: page 6]

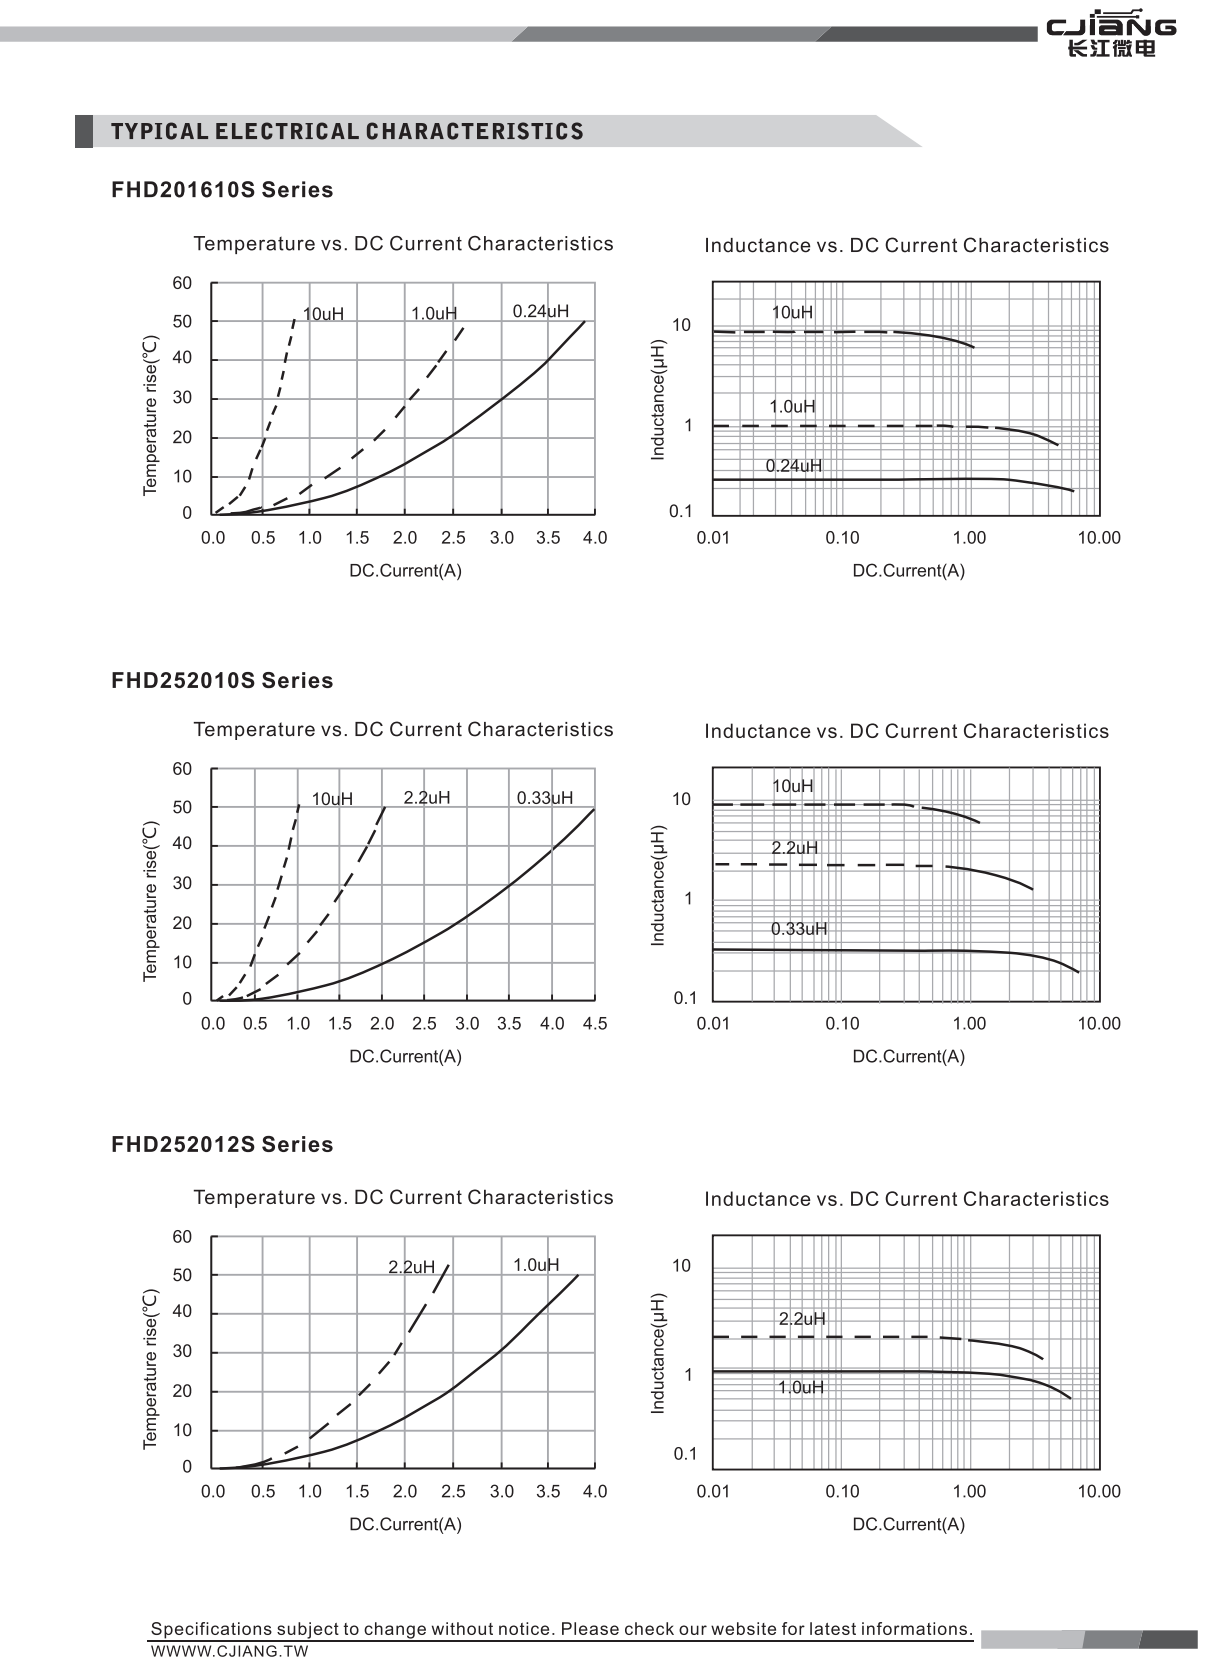
[picture p151: page 7]

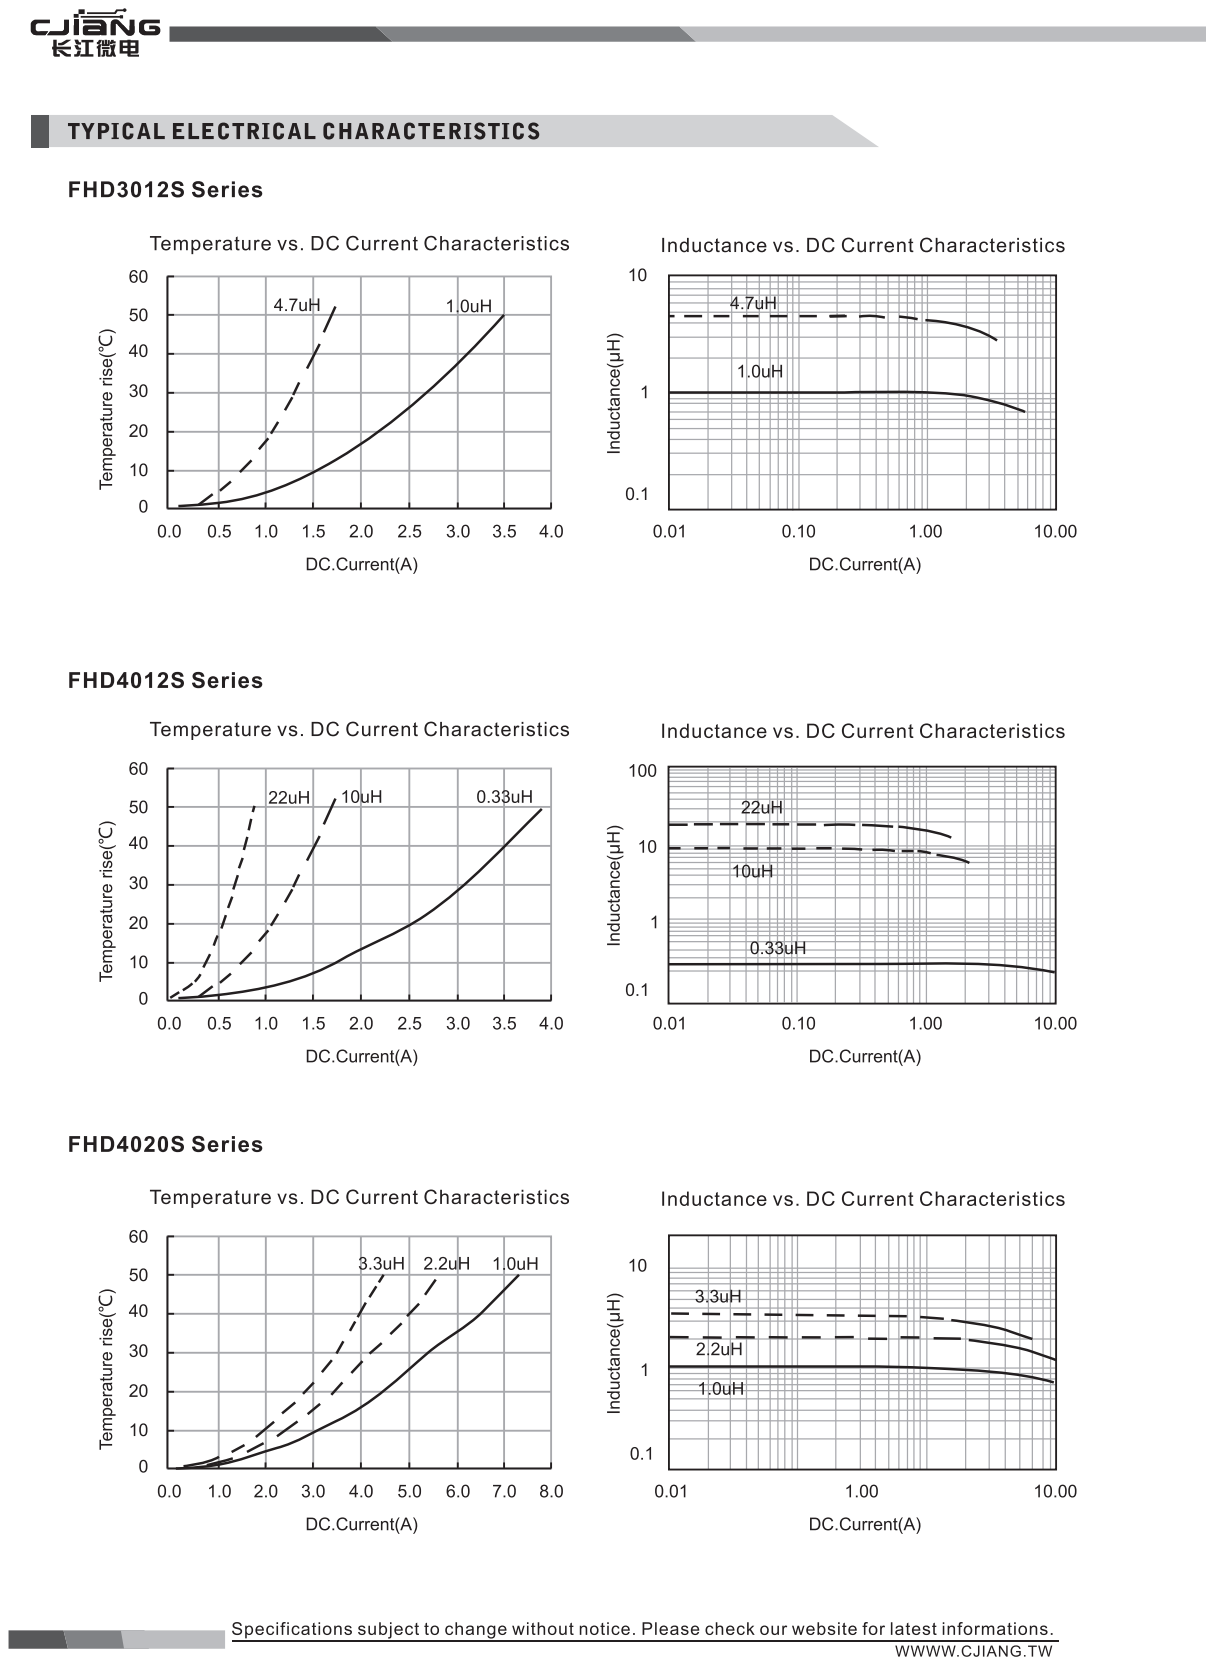
[picture p152: page 8]
