esp-cpp/esp-box-emu/ecad/Box Electronics v25.pdf

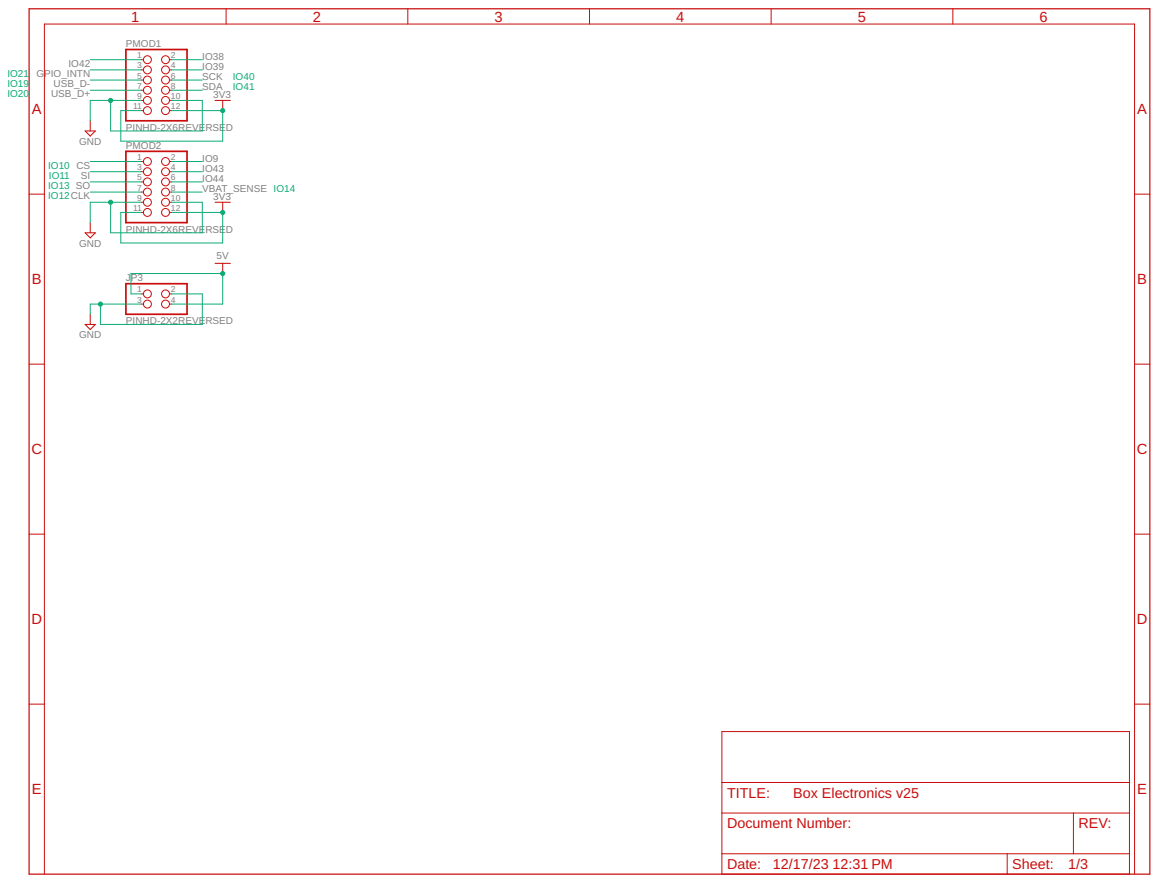
[picture p153: page 1]

Document Number: | REV:

Date: 12/17/23 12:31 PM | Sheet: 1/3

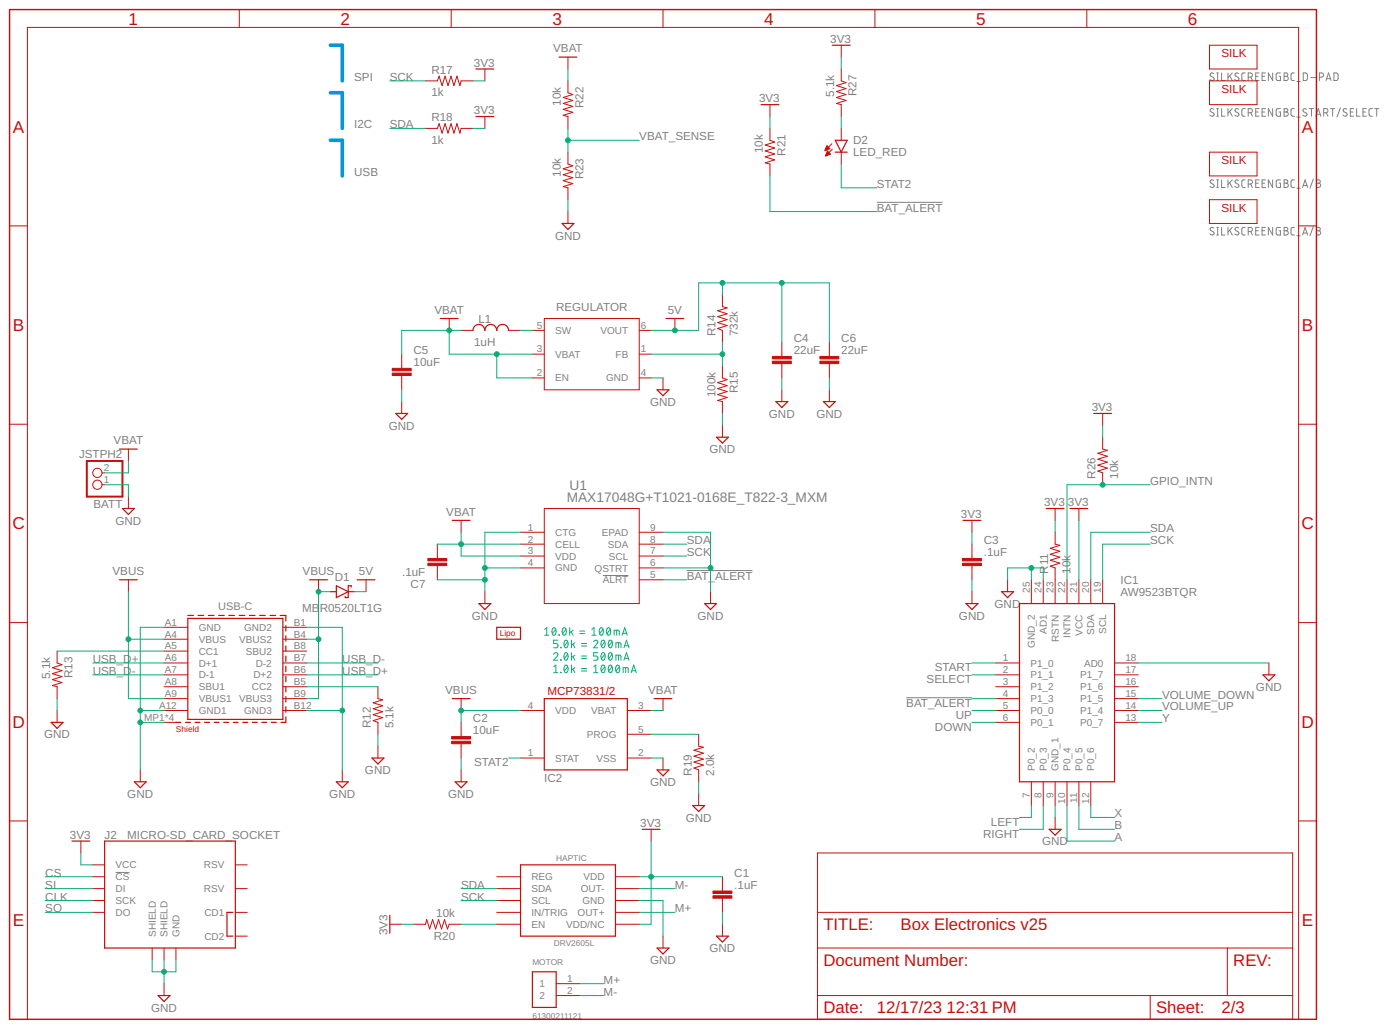
[picture p154: page 2]

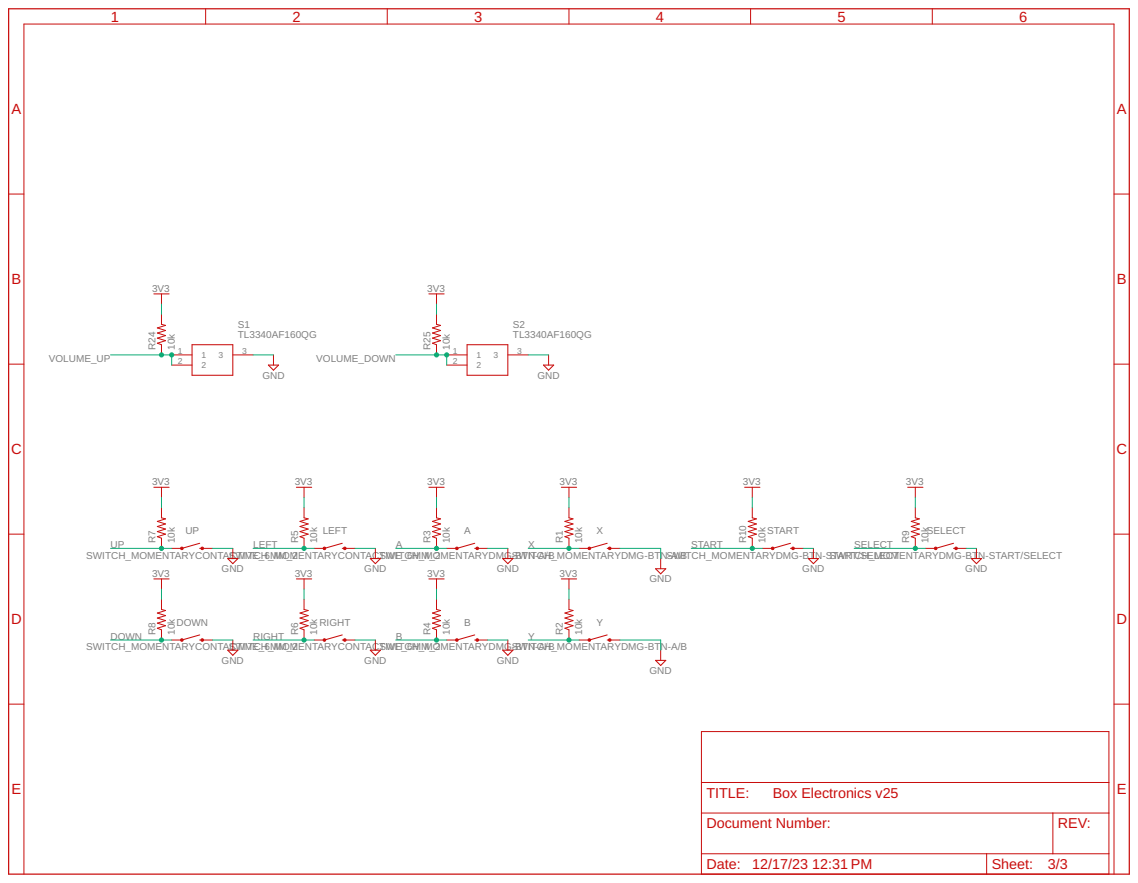
[picture p155: page 3]

SWITCH_MOMENTARYDMG-BTN-SSTWARITTC/SHE_LMEOCMTENTARYDMG-BTN-START/SELECT
