esp-cpp/esp-box-emu/ecad/Box-3 Electronics v5.pdf

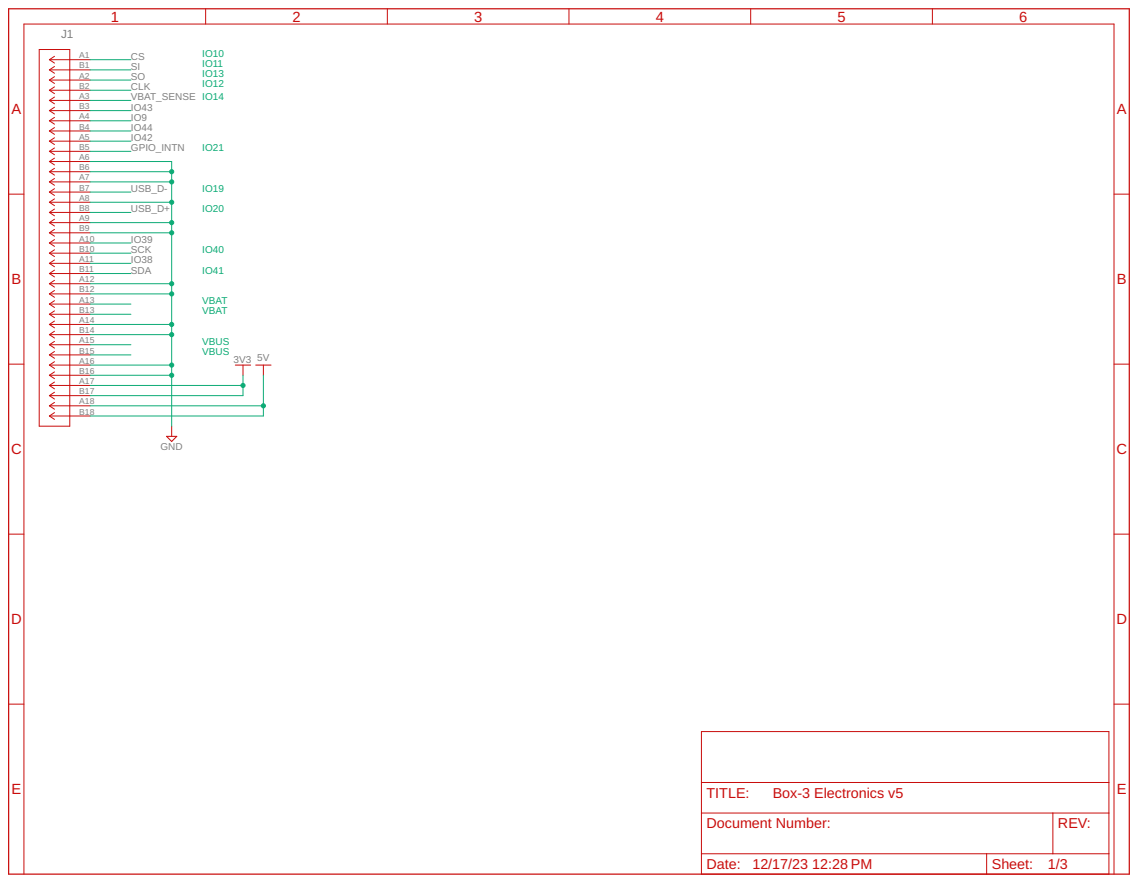
[picture p156: page 1]

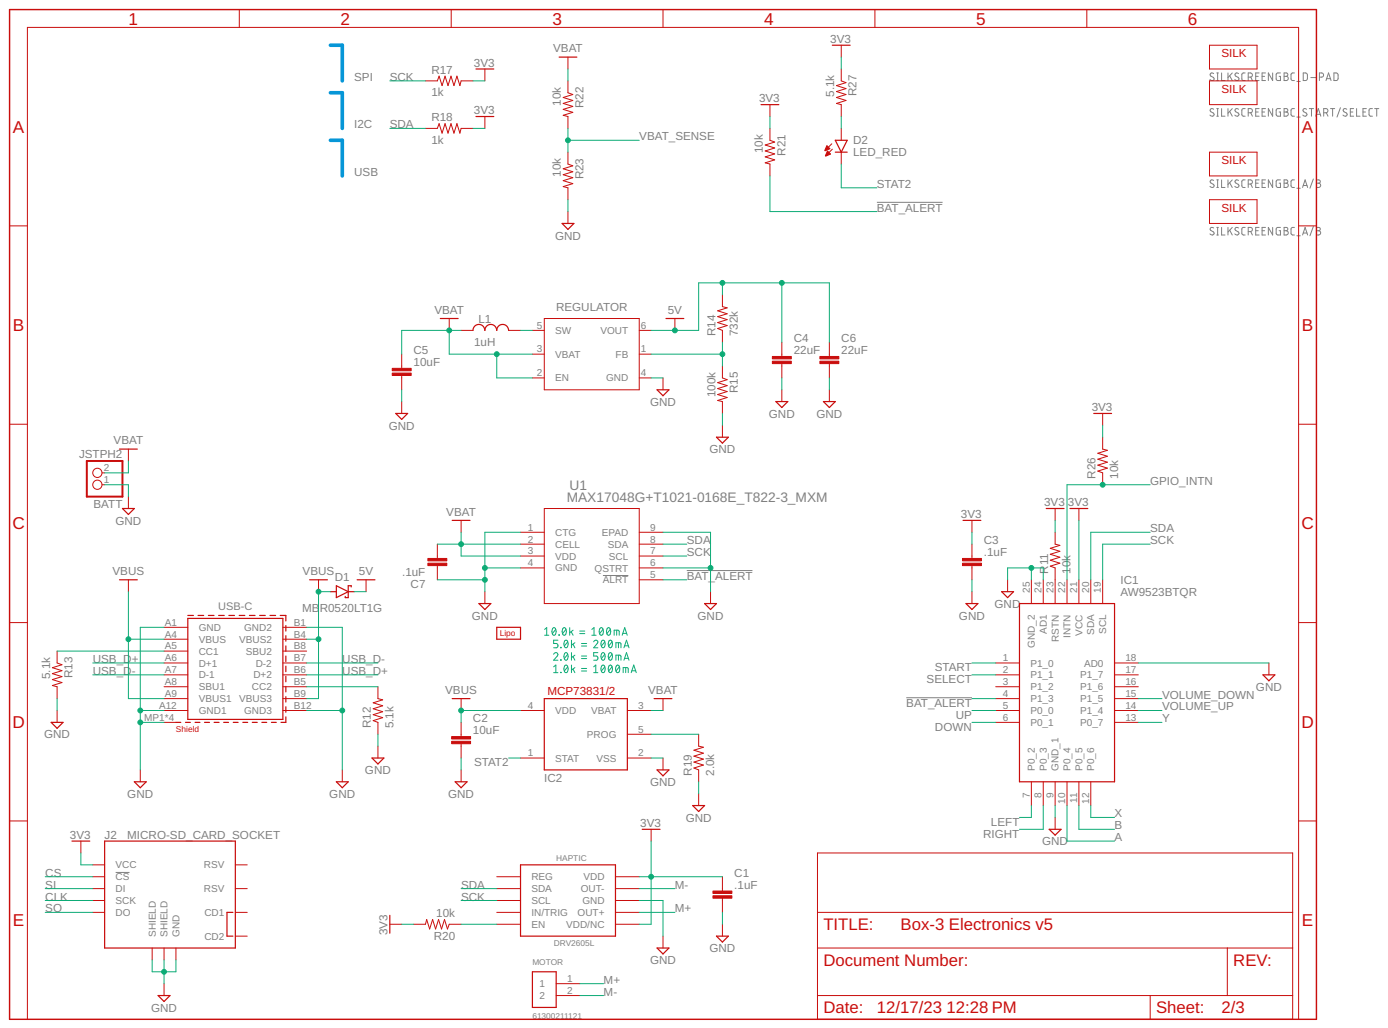
[picture p157: page 2]

Document Number: | REV:

Date: 12/17/23 12:28 PM | Sheet: 2/3

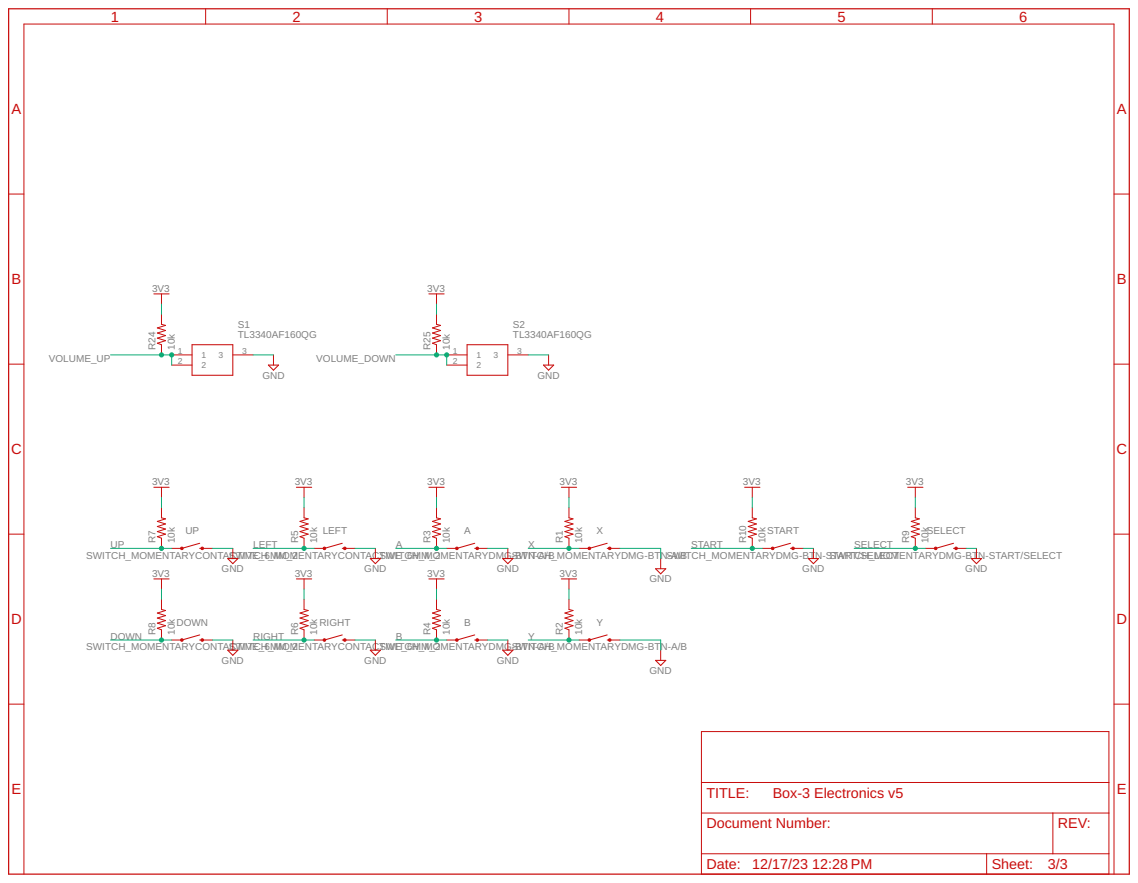
[picture p158: page 3]

SWITCH_MOMENTARYDMG-BTN-SSTWARITTC/SHE_LMEOCMTENTARYDMG-BTN-START/SELECT

Document Number: | REV:

Date: 12/17/23 12:28 PM | Sheet: 3/3
